Ajimaru/OctoScale/assets/stl-previews/OctoScale_Top.png

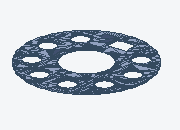
assets/stl-previews/OctoScale_Top.png
