Ajimaru/OctoScale/assets/stl-previews/OctoScaleBottom.png

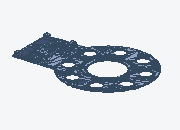
assets/stl-previews/OctoScaleBottom.png
