Ajimaru/OctoScale/assets/stl-previews/OctoScaleScreenBazel.png

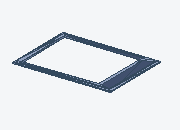
assets/stl-previews/OctoScaleScreenBazel.png
