Ajimaru/OctoScale/hardware/OctoScale-Wiring/OctoScale-Wiring.kicad_sch

## KiCad design hardware/OctoScale-Wiring/OctoScale-Wiring.kicad_sch (2026-09-16)

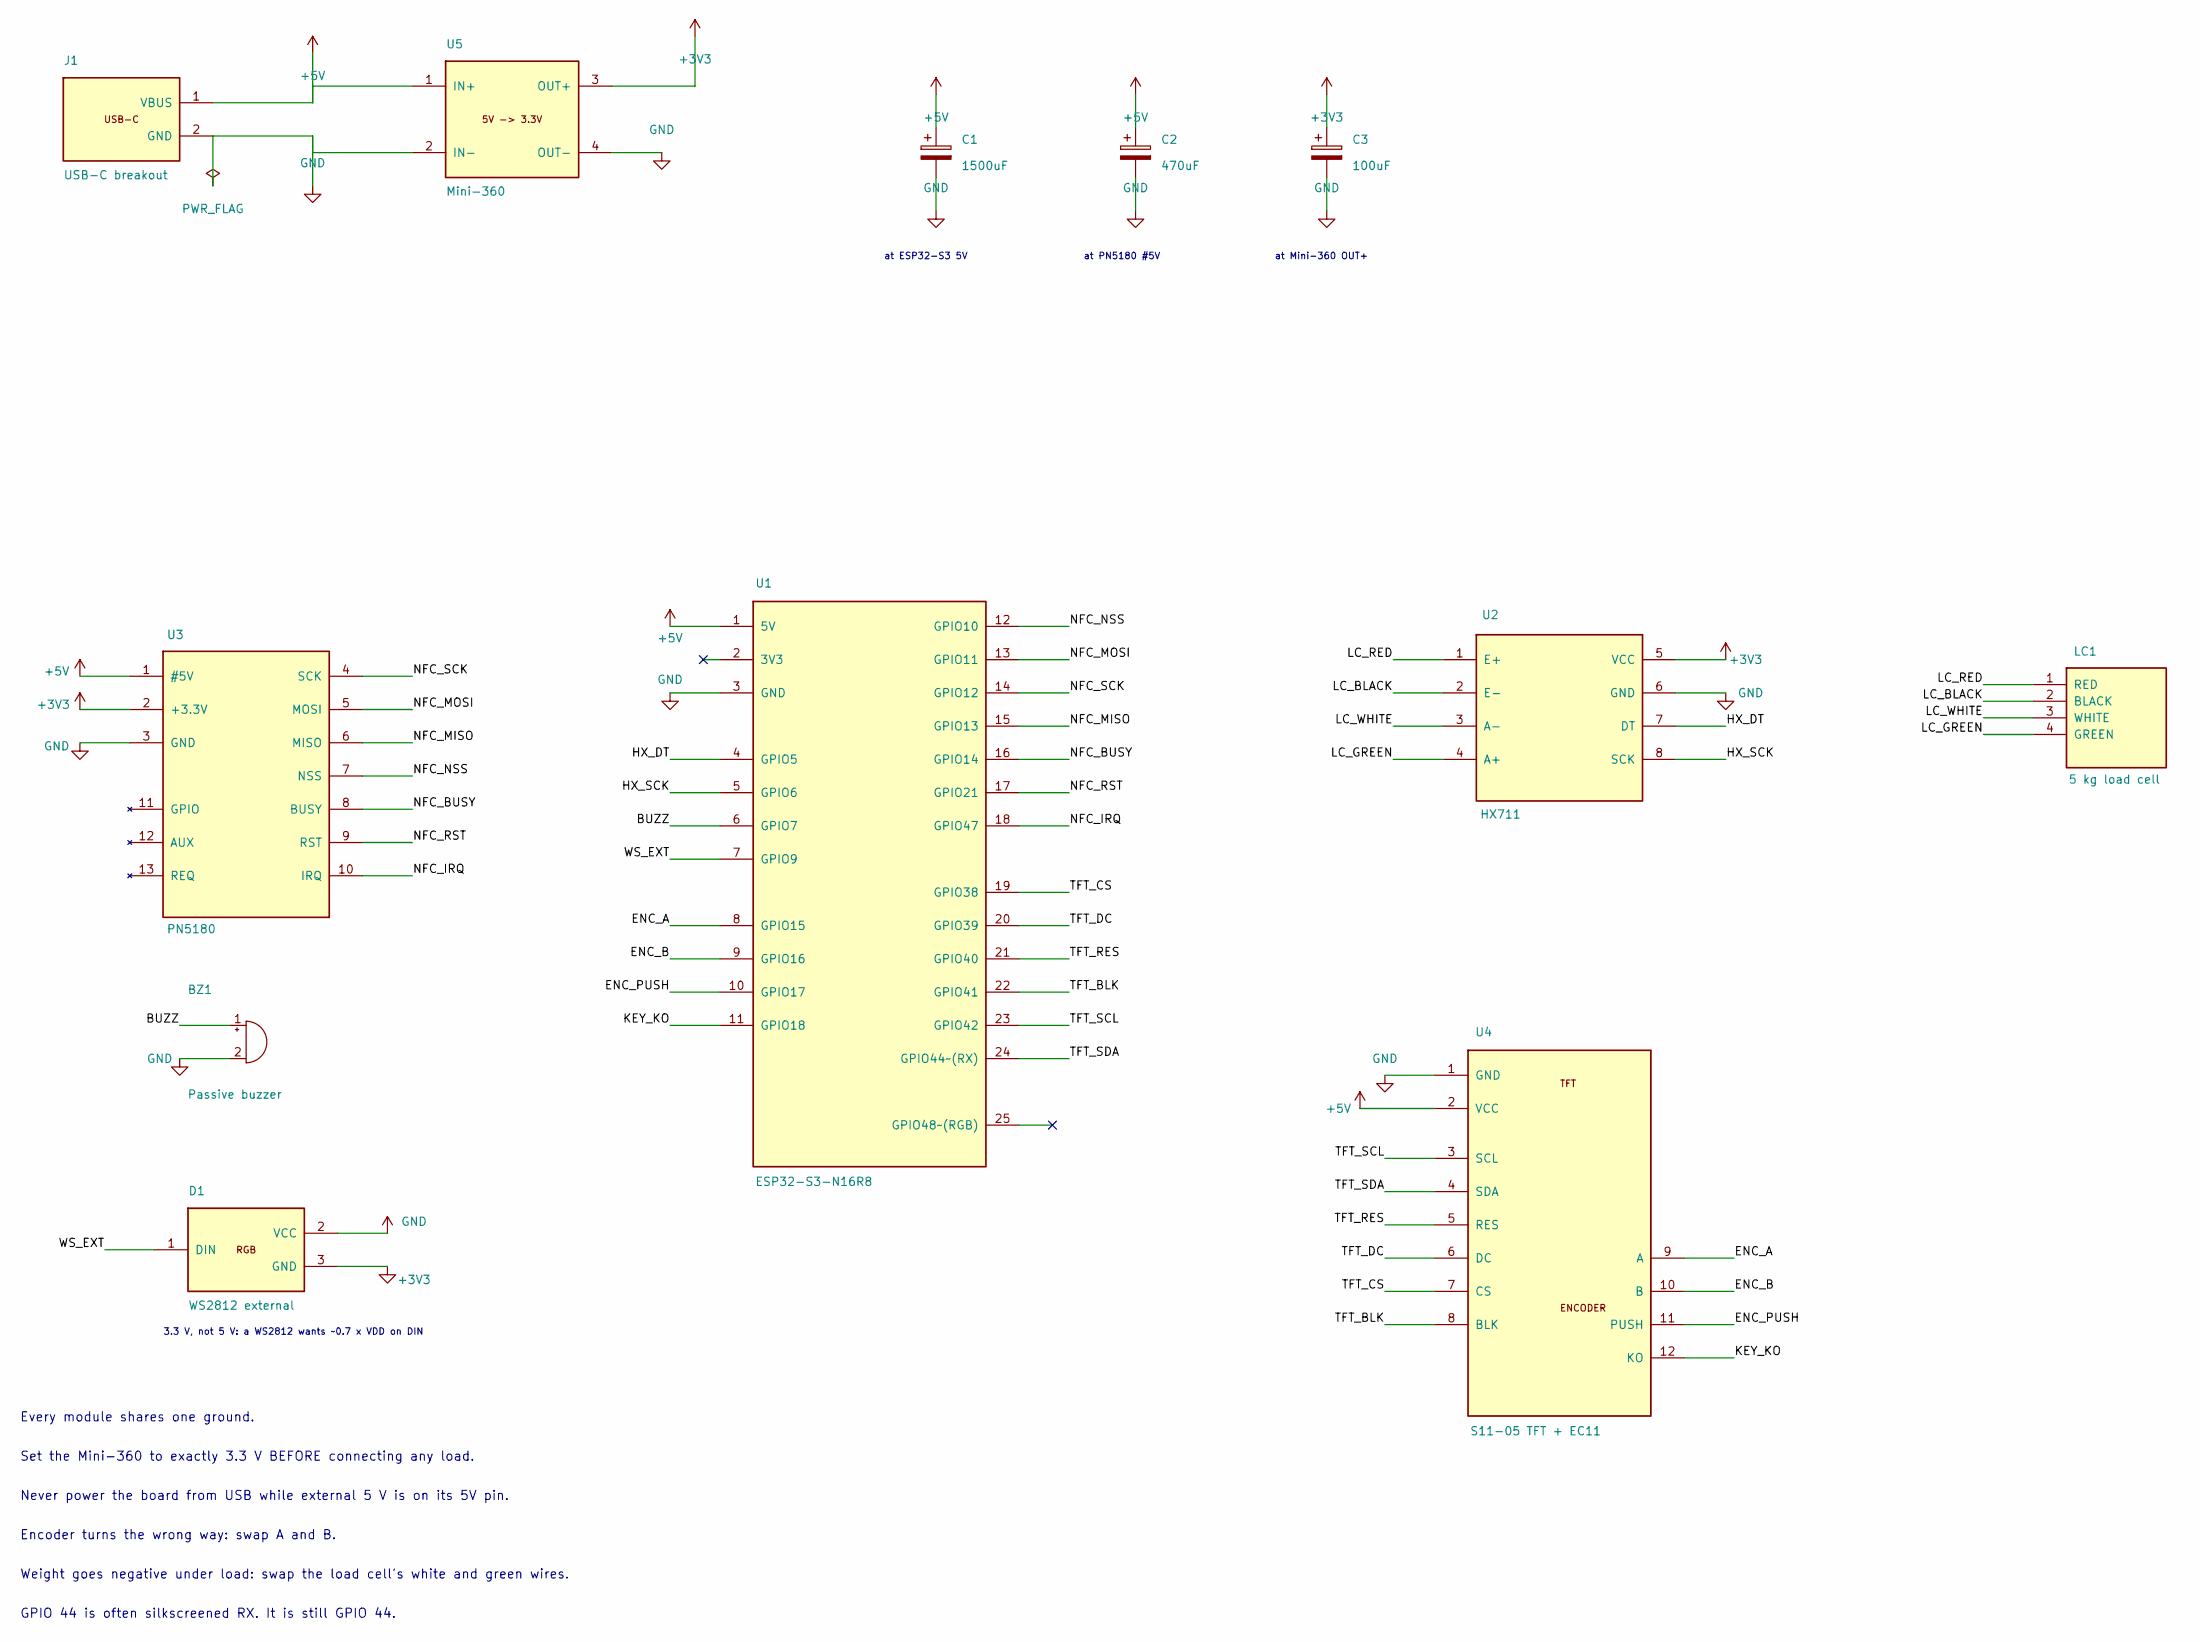
[picture p30: schematic OctoScale-Wiring.kicad_sch]

Parts:
BZ1: Passive buzzer
C1: 1500uF
C2: 470uF
C3: 100uF
D1: WS2812 external
J1: USB-C breakout
LC1: 5 kg load cell
U1: ESP32-S3-N16R8
U2: HX711
U3: PN5180
U4: S11-05 TFT + EC11
U5: Mini-360

Connections:
+3V3: C3.1, D1.2 (VCC), U2.5 (VCC), U3.2 (+3.3V), U5.3 (OUT+)
+5V: C1.1, C2.1, J1.1 (VBUS), U1.1 (5V), U3.1 (#5V), U4.2 (VCC), U5.1 (IN+)
BUZZ: BZ1.1 (+), U1.6 (GPIO7)
ENC_A: U1.8 (GPIO15), U4.9 (A)
ENC_B: U1.9 (GPIO16), U4.10 (B)
ENC_PUSH: U1.10 (GPIO17), U4.11 (PUSH)
GND: BZ1.2 (-), C1.2, C2.2, C3.2, D1.3 (GND), J1.2 (GND), U1.3 (GND), U2.6 (GND), U3.3 (GND), U4.1 (GND), U5.2 (IN-), U5.4 (OUT-)
HX_DT: U1.4 (GPIO5), U2.7 (DT)
HX_SCK: U1.5 (GPIO6), U2.8 (SCK)
KEY_KO: U1.11 (GPIO18), U4.12 (KO)
LC_BLACK: LC1.2 (BLACK), U2.2 (E-)
LC_GREEN: LC1.4 (GREEN), U2.4 (A+)
LC_RED: LC1.1 (RED), U2.1 (E+)
LC_WHITE: LC1.3 (WHITE), U2.3 (A-)
NFC_BUSY: U1.16 (GPIO14), U3.8 (BUSY)
NFC_IRQ: U1.18 (GPIO47), U3.10 (IRQ)
NFC_MISO: U1.15 (GPIO13), U3.6 (MISO)
NFC_MOSI: U1.13 (GPIO11), U3.5 (MOSI)
NFC_NSS: U1.12 (GPIO10), U3.7 (NSS)
NFC_RST: U1.17 (GPIO21), U3.9 (RST)
NFC_SCK: U1.14 (GPIO12), U3.4 (SCK)
TFT_BLK: U1.22 (GPIO41), U4.8 (BLK)
TFT_CS: U1.19 (GPIO38), U4.7 (CS)
TFT_DC: U1.20 (GPIO39), U4.6 (DC)
TFT_RES: U1.21 (GPIO40), U4.5 (RES)
TFT_SCL: U1.23 (GPIO42), U4.3 (SCL)
TFT_SDA: U1.24 (GPIO44~(RX)), U4.4 (SDA)
WS_EXT: D1.1 (DIN), U1.7 (GPIO9)

Notes on the sheet:
Weight goes negative under load: swap the load cell's white and green wires.
Set the Mini-360 to exactly 3.3 V BEFORE connecting any load.
at PN5180 #5V
Every module shares one ground.
at ESP32-S3 5V
Never power the board from USB while external 5 V is on its 5V pin.
Encoder turns the wrong way: swap A and B.
GPIO 44 is often silkscreened RX. It is still GPIO 44.
at Mini-360 OUT+
3.3 V, not 5 V: a WS2812 wants ~0.7 x VDD on DIN
