Ajimaru/OctoScale/src/pn5180nfc.h

#pragma once
#include <Arduino.h>

// pn5180nfc.h — PN5180 NFC reader (SPI) via the atrappmann/PN5180 library.
//
// FSPI bus (global SPI, SCK=12/MOSI=11/MISO=13), dedicated control pins
// (NSS=10/BUSY=14/RST=21). The chip answers over MISO, so the EEPROM version read
// confirms bus + chip + wiring all work.

// --- Tag types (protocol-neutral) ---
enum PN5180TagType {
  PN5180_TAG_NONE = 0,   // no tag in the field
  PN5180_TAG_NFCV,       // ISO15693 / NFC-V
  PN5180_TAG_NFCA,       // ISO14443-A / NFC-A
};

// Result of a debug probe (latest state, readable via HTTP).
struct PN5180ProbeResult {
  PN5180TagType type = PN5180_TAG_NONE;
  String uid = "";       // big-endian hex (usual display order)
  uint16_t atqa = 0;     // NFC-A only: ATQA (2 bytes)
  uint8_t sak = 0;       // NFC-A only: SAK (1 byte, type hint)
  uint8_t blockSize = 0; // NFC-V only: bytes/block (from getSystemInfo, 0 = unknown)
  uint8_t numBlocks = 0; // NFC-V only: block count (from getSystemInfo, 0 = unknown)
  uint8_t dsfid = 0;      // NFC-V only: Data Storage Format Identifier, if the tag reports one
  bool dsfidPresent = false;
  uint8_t afi = 0;        // NFC-V only: Application Family Identifier, if the tag reports one
  bool afiPresent = false;
  // NFC-V only: manufacturer-specific IC reference byte. Shown as a raw hex value, not
  // decoded to a chip name -- no verified public mapping of this byte to NXP ICODE
  // variants (SLI/SLIX/SLIX2/SLIX-L/...) was found; guessing wrong would be worse than
  // not showing a product name at all (see HARDWARE.md's "Tags evaluated for NFC-V").
  uint8_t icRef = 0;
  bool icRefPresent = false;
  int numPages = 0;       // NFC-A only: page/block count (Mifare Classic: fixed 64; NTAG: from GET_VERSION)
  bool numPagesPresent = false;
  long idParsed = -1;    // databaseId parsed off the tag's data area (-1 = none/unparsable)
  String idText = "";    // raw characters read where the databaseId would be (debug only)
  // How much the idParsed above can be trusted -- the legacy ID layout carries no magic
  // and no checksum, so "there are digits at the right offset" is NOT proof the tag is
  // ours. Consumers (the load flow, the SpoolManager plugin) need to tell the two apart:
  //   "extended" -- id came from a self-describing format (ntagExtended's "OX" magic,
  //                 octoscaleExtended's "OS", nfcvExtended, OpenSpool NDEF, TigerTag).
  //                 A magic matched, so the id is as trustworthy as the format itself.
  //   "legacy"   -- id came from the header-less ASCII field written by /nfcwriteid
  //                 (pn5180WriteNtagId & friends). Shape-validated only. A foreign tag
  //                 with digits in the same place is indistinguishable from ours.
  //   "unverified" -- as "legacy", AND the tag's occupancy says "foreign": the CC/data
  //                 area belongs to a format we did not write. Almost certainly not our
  //                 id. Callers should refuse to act on it without asking the user.
  //   "extendedNoId" -- a verified format that carries no OctoScale databaseId at all
  //                 (TigerTag, OpenPrintTag). Structured data IS present, so this is
  //                 NOT the same as "": a caller must not treat the tag as blank.
  //   ""         -- no id parsed at all (idParsed == -1).
  // Set by pn5180ApplyIdTrust() once occupancy is known; the raw read paths only ever
  // produce "extended" or "legacy", since they cannot see the CC.
  String idSource = "";
  // Capability Container state (NFC-A/NTAG + NFC-V only -- Mifare Classic has no CC
  // concept, stays ""). "virgin" = all-zero, never written; "ndef" = valid NDEF CC
  // (0xE1/0xE2 magic) -- the OTP bit is set and can NEVER be unset again, even by an
  // erase (see pn5180NtagCcIsVirgin/pn5180NfcvCcIsVirgin, and pn5180EraseTag's
  // comment); "other" = neither (foreign/non-NDEF content, erase/write would refuse
  // to touch it); "" = not read (Mifare, or read failed).
  String ccState = "";
  // False while a tag has been detected but its Extended read / occupancy probes have
  // not finished yet. The poll loop publishes type and uid as soon as the tag answers,
  // because the TFT needs them immediately, but the id and the format fields are only
  // filled a few hundred milliseconds later. Without this flag that window is
  // indistinguishable from a finished read of a tag that genuinely has no id, so a
  // caller polling once could see an Extended tag as "empty, no id" and offer to
  // overwrite it. A caller that only acts on complete data should require this.
  bool complete = false;
};

// databaseId storage on the tag (uniformly ASCII decimal):
//  - NFC-A/NTAG: user pages starting at page 4 (READ 0x30 always returns 4 pages/16 B).
//  - NFC-V/ISO15693: blocks starting at block 0 (readSingleBlock, usually 4 B/block).
// 12 bytes covers the full uint32 range (max 10 digits) + terminator.
static const uint8_t PN5180_ID_START_PAGE = 4;   // NFC-A: first user page
static const uint8_t PN5180_ID_START_BLOCK = 0;  // NFC-V: first data block
static const uint8_t PN5180_ID_BYTES = 12;       // 12 bytes ASCII decimal

// --- Mifare Classic 1K (blank/factory tags only -- see pn5180nfc.h's mifare section) --
// Block 4 = sector 1's first data block: sector 0 (blocks 0-3) holds the manufacturer
// block + often factory data, so sector 1 is the first "clean" sector on every blank
// 1K tag. One 16-byte block comfortably fits PN5180_ID_BYTES (12) -> no multi-block
// split needed, unlike NTAG's 4-byte pages.
static const uint8_t MIFARE_ID_BLOCK = 4;
static const uint8_t MIFARE_KEY_A[6] = {0xFF, 0xFF, 0xFF, 0xFF, 0xFF, 0xFF};  // factory default
static const uint8_t MIFARE_AUTH_KEY_A = 0x60;
static const uint8_t MIFARE_AUTH_KEY_B = 0x61;  // foreign tags may guard data with B

// --- Mifare Classic Extended layout (plan C.1) --------------------------------
// Sector 1 (block 4, unchanged) stays the legacy ID anchor. Sector 2 (blocks 8-9) adds
// numeric fields + a CRC-8 "commit marker" (block 8's magic). Sector 3 (blocks 12-14)
// adds strings. Block 8 is written LAST -- an aborted write leaves a tag with no magic,
// which reads back as "legacy ID only", never as a corrupt Extended payload.
static const uint8_t MIFARE_EXT_MAGIC0 = 'O';
static const uint8_t MIFARE_EXT_MAGIC1 = 'S';
// v3: sector 4 block 16 adds 7 more numeric fields (remainingWeight/totalLength/
// usedLength/firstUse/lastUse/purchasedOn/cost), sectors 5-8 (12 blocks) add a
// second, longer string buffer (code/batchNumber/purchasedFrom/finish/displayName),
// sector 9 block 36 is a v3-only commit marker (own sub-magic, checked independently
// of block 8's) so a v3 reader can tell "v3 fields genuinely present and intact" apart
// from "v3 version byte was set but the write was cut off before the new blocks
// landed" -- block 8 is still written LAST overall, same discipline as v1/v2.
static const uint8_t MIFARE_EXT_VERSION = 0x05;  // v5: drying/td in block 17[6..11] (v4: multi-colour in block 10[2..8])
static const uint8_t MIFARE_EXT_BLOCK8  = 8;
static const uint8_t MIFARE_EXT_BLOCK9  = 9;
static const uint8_t MIFARE_EXT_BLOCK10 = 10;  // v2+: [0] bed temp min [1] bed temp max
static const uint8_t MIFARE_EXT_BLOCK12 = 12;
static const uint8_t MIFARE_EXT_BLOCK13 = 13;
static const uint8_t MIFARE_EXT_BLOCK14 = 14;
static const int MIFARE_EXT_STRING_BYTES = 48;  // blocks 12-14, 16 bytes each
static const uint8_t MIFARE_EXT_BLOCK16 = 16;   // v3: sector 4, 7 packed numeric fields
// Block 16 is packed full (all 16 bytes), so the minute-of-day companions for
// firstUse/lastUse/purchasedOn get block 17 -- same sector, so it rides along on the
// auth block 16 already did, no extra Crypto1 round.
static const uint8_t MIFARE_EXT_BLOCK17 = 17;   // v3: 3x minute-of-day (uint16 LE);
                                               // v5: +6 dryTemp u8, +7 pad, +8 dryTime u16 LE,
                                               // +10 td x100 u16 LE, +12..15 reserved 0x00
// v3 string buffer: sectors 5-8, 12 contiguous data blocks treated as one flat
// 192-byte length-prefixed buffer (same [1-byte len][UTF-8 bytes] convention as the
// existing 3-string block above, just longer/more records). Block numbers skip each
// sector's trailer (23,27,31,35 are Crypto1 key blocks, not data).
static const uint8_t MIFARE_EXT_BLOCK20 = 20;
static const int MIFARE_EXT_STRING2_BLOCKS[12] = {20,21,22, 24,25,26, 28,29,30, 32,33,34};
static const int MIFARE_EXT_STRING2_BYTES = 192;  // 12 blocks x 16 B
static const uint8_t MIFARE_EXT_BLOCK36 = 36;   // v3: sector 9, commit marker

// --- NFC-V/ISO15693 Extended layout (blank/user-purchased tags only, same caveat as
// Mifare above -- this is NOT written to a tag whose blocks might already hold
// factory/vendor data; pn5180WriteNfcvSpoolTag only ever gets called for tags the
// user chose to write a spool ID to via the web UI in the first place). --------------
// Fixed 4-byte blocks (pn5180WriteNfcvId's own reasoning: getSystemInfo() has a known
// OOB-read bug on short/non-conforming replies, so it's never queried for this format
// either -- 4 B/block is the documented fallback and covers the ICODE-family tags this
// project targets). Blocks 0-2 stay the legacy 12-byte ID anchor (unchanged). Same
// commit-marker discipline as Mifare: the magic block is written LAST.
//   Block 3-4  (8 B):  magic(2) + version(1) + flags(1) + databaseId(4, uint32 LE)
//   Block 5-6  (8 B):  totalWeight/spoolWeight/usedWeight (uint16 LE each) + density (uint16 LE)
//   Block 7-10 (16 B): diameter+diameterTolerance (uint16 LE each) + 3 temps (uint8) +
//                      3 signed offsets (int8) + RGB (3 B) + hotend temp min/max (uint8 each,
//                      v2+) + CRC-8 (1 B, over blocks 3-10 minus the CRC byte itself)
//   Block 11-22 (48 B): strings (vendor/material/colorName), same length-prefixed layout as Mifare
//   Block 23 (4 B, v2+): [0] bed temp min (uint8) [1] bed temp max (uint8) [2-3] reserved
static const uint8_t NFCV_EXT_MAGIC0 = 'O';
static const uint8_t NFCV_EXT_MAGIC1 = 'S';
static const uint8_t NFCV_EXT_VERSION = 0x04;  // v4: drying/td in blocks 26-27 (v3: multi-colour in blocks 24-25)
static const uint8_t NFCV_EXT_BLOCK_START = 3;   // magic/version/flags/dbId: blocks 3-4
static const uint8_t NFCV_EXT_BLOCK_NUM   = 5;   // weights/density: blocks 5-6
static const uint8_t NFCV_EXT_BLOCK_PHYS  = 7;   // diameter/temps/rgb/crc: blocks 7-10
static const uint8_t NFCV_EXT_BLOCK_STR   = 11;  // strings: blocks 11-22
static const int NFCV_EXT_STRING_BYTES = 48;
static const uint8_t NFCV_EXT_BLOCK_TEMPRANGE = 23;  // v2+: bed temp min/max (4 B block)
// v3: multi-colour. tempRangeBuf has only [2..3] free -- not enough for 2 RGB trios plus
// flags -- so this takes two fresh blocks from the tag's unused tail (24-27 are free on
// the smallest ICODE this project targets, 28 blocks / 112 B). Colour 1 stays in
// physBuf where it always was.
static const uint8_t NFCV_EXT_BLOCK_COLOR = 24;   // [0..2] colour 2, [3] flags
                                                  // block 25: [0..2] colour 3, [3] reserved
// v4: drying/td. Strings live in blocks 11-22, i.e. BEFORE these -- unlike NTAG, adding
// them shifts nothing, so no existing field can be misread if a writer gets it wrong.
static const uint8_t NFCV_EXT_BLOCK_DRY = 26;    // [0] dryTemp u8, [1] pad, [2..3] dryTime u16 LE
                                                  // block 27: [0..1] td x100 u16 LE, [2..3] reserved
static const uint8_t NFCV_BLOCK_SIZE = 4;

// --- NTAG Extended layout (NTAG215/216 only -- 213's ~144 B usable can't fit the v3
// field set, see the capacity comment on pn5180WriteNtagExtended; offered as a
// SpoolManagerExtended write-format preference alongside openSpool, mirroring NFC-V's existing
// nfcvExtended/nfcvOpenSpool choice). No NDEF wrapper (Extended isn't meant to be read
// by a generic phone NFC app, same reasoning as Mifare's own Extended format) -- pages
// are written directly starting at page 4 (the first user page; pages 0-3 are
// UID/lock/CC/internal and never touched). Single version, full v3 field set from the
// start (no v1/v2 predecessor to stay compatible with, unlike Mifare/NFC-V). All 20
// fixed-layout bytes below are 4-byte-page-aligned (5 pages, 4-19 is NOT used -- pages
// 4-8, 20 B total) -------------------------------------------------------------------
//   Pages 4-5   (8 B):  magic(2) + version(1) + flags(1) + databaseId(4, uint32 LE)
//   Pages 6-7   (8 B):  totalWeight/spoolWeight/usedWeight/remainingWeight (uint16 LE each)
//   Page 8      (4 B):  density(uint16 LE) + diameter(uint16 LE)
//   Pages 9-11  (12 B): diameterTolerance(uint16 LE) + 3 temps(uint8) + 3 signed
//                       offsets(int8) + RGB(3 B) + temperatureMax(uint8)
//   Page 12     (4 B):  temperatureMin/bedTemperatureMin/bedTemperatureMax(uint8 each)
//                       + reserved(1 B)
//   Page 13     (4 B):  CRC-8(1 B, over pages 4-12 + this page's first byte, i.e. all
//                       fixed numeric bytes before it) + reserved(3 B)
//   Pages 14-16 (12 B): totalLength/usedLength (uint24 LE each, 6 B) + cost (uint16 LE,
//                       fixed-point x100, 2 B) + firstUse(uint16 LE, 2 B) + reserved(2 B)
//   Pages 17-18 (8 B):  lastUse/purchasedOn (uint16 LE each, days since 1970-01-01)
//   Pages 19+   :       8 length-prefixed strings (vendor/material/colorName/code/
//                       batchNumber/purchasedFrom/finish/displayName), same
//                       [1-byte len][UTF-8 bytes] convention as Mifare/NFC-V, flat
//                       across as many pages as the tag's capacity allows
//   Last page used: commit marker, own sub-magic ('N','X') + flags2 bit0 ("strings
//                       present") -- written LAST, same discipline as every other
//                       Extended format: an aborted write never reads back as corrupt,
//                       only as "no Extended data" (magic missing) or "numeric fields
//                       only, no strings" (commit marker missing/incomplete).
static const uint8_t NTAG_EXT_MAGIC0 = 'O';
static const uint8_t NTAG_EXT_MAGIC1 = 'X';
static const uint8_t NTAG_EXT_VERSION = 0x03;  // v3: drying/td on pages 21-22 (v2: multi-colour on pages 19-20)
static const uint8_t NTAG_EXT_PAGE_START = 4;    // magic/version/flags/dbId: pages 4-5
static const uint8_t NTAG_EXT_PAGE_NUM   = 6;    // totalWeight/spoolWeight/usedWeight/remainingWeight: pages 6-7
static const uint8_t NTAG_EXT_PAGE_DENSITY = 8;  // density+diameter: page 8
static const uint8_t NTAG_EXT_PAGE_PHYS  = 9;    // diameterTolerance/temps/offsets/rgb/temperatureMax: pages 9-11
static const uint8_t NTAG_EXT_PAGE_TEMPMIN = 12; // temperatureMin/bedTemperatureMin/Max: page 12
static const uint8_t NTAG_EXT_PAGE_CRC   = 13;   // CRC-8: page 13
static const uint8_t NTAG_EXT_PAGE_LEN   = 14;   // totalLength/usedLength/cost/firstUse: pages 14-16
static const uint8_t NTAG_EXT_PAGE_DATES = 17;   // lastUse/purchasedOn: pages 17-18
static const uint8_t NTAG_EXT_PAGE_COLOR = 19;  // v2: [0..2] colour 2, [3] flags
                                                // page 20: [0..2] colour 3, [3] reserved
// v3: pages 21-22 carry drying/td, so the string buffer moves 21 -> 23. This constant is
// the single source of truth for that boundary -- fixedBuf's size, the string budget, the
// pad loop and the commit-marker scan are all derived from it, so moving it moves them
// all together. Leaving strings at 21 while writing v3 would produce a complete,
// valid-LOOKING tag with the drying bytes read back as vendor/material.
static const uint8_t NTAG_EXT_PAGE_STR   = 23;  // strings start here (19 pre-v2, 21 in v2)
static const uint8_t NTAG_EXT_PAGE_DRY   = 21;  // v3: [0] dryTemp u8, [1] pad, [2..3] dryTime u16 LE
                                                //     page 22: [0..1] td x100 u16 LE, [2..3] reserved
static const uint8_t NTAG_EXT_MAGIC2_0 = 'N';    // commit marker sub-magic (last page)
static const uint8_t NTAG_EXT_MAGIC2_1 = 'X';
// CRC coverage: pages 4-12 (36 B) + page 13's own first byte position is the CRC
// itself, so coverage is exactly pages 4-12 -- 9 pages x 4 B = 36 B.
static const int NTAG_EXT_CRC_LEN = (NTAG_EXT_PAGE_CRC - NTAG_EXT_PAGE_START) * 4;

// --- TigerTag Standard layout (foreign format, NOT our own -- byte-for-byte per the
// TigerTag-SDK-Python, Apache-2.0, tigertag/tag.py, as relayed by the SpoolManagerExtended
// peer session and cross-checked against their own tested read-parser). All
// multi-byte fields BIG-ENDIAN, unlike every OctoScale-native NTAG/Mifare layout
// above (little-endian) -- do not reuse pn5180ScaleU16/pn5180ScaleU24 here, their
// byte order is wrong for this format.
//
// Payload is exactly 80 bytes (pages 4-23, NTAG213-sized, unsigned/"Standard"
// variant) -- offsets below are relative to page 4 = byte 0. Bytes 32+ (Twin-Tag-ID,
// Color 2/3, TD, custom message, measure-available) are NOT written: no verified
// SDK source for their layout was available at implementation time (see the
// TigerTag write-support conversation) -- leaving them zeroed is the deliberate
// choice over guessing.
static const uint8_t TIGERTAG_PAGE_START = 4;
static const uint32_t TIGERTAG_MAGIC_STANDARD = 0x5BF59264;  // unsigned, what we write
// static const uint32_t TIGERTAG_MAGIC_PLUS = 0xBC0FCB97;  // signed variant -- never
// written here, would need a private key we don't have.
static const uint32_t TIGERTAG_PRODUCT_ID_GENERIC = 0xFFFFFFFF;  // "offline"/no catalog link
static const int TIGERTAG_PAYLOAD_LEN = 80;                      // bytes, pages 4-23

// Data carried between the HTTP handler (POST /nfcwritespool) and the write functions.
// Optional fields use hasX flags (JSON may omit some) -- unset numeric fields are
// written as their "not set" sentinel (0xFFFF for uint16 scaled fields, matching the
// existing octoprint.h convention of -1 meaning "not set").
struct SpoolTagData {
  long databaseId = -1;
  String material = "", vendor = "", colorName = "";
  String color = "";       // "#rrggbb" or "#rrggbb;#rrggbb..." or "rainbow"/"transparent..."
  // v4 multi-color: SpoolManagerExtended's `color` field is a small grammar, not a hex
  // string -- "[transparent:]#hex[;#hex[;#hex]]" or the bare sentinel "rainbow" (see
  // its SPOOLMANAGER_UTILS.composeSpoolColor/parseSpoolColor). Up to THREE colours (the
  // UI has three pickers), plus two independent flags. Earlier formats stored only the
  // first colour and dropped the rest silently; these fields carry the whole value.
  // colorCount 0 with isTransparent set is legitimate ("transparent", untinted).
  uint8_t colorRgb[3][3] = {{0,0,0},{0,0,0},{0,0,0}};  // up to 3 colours, RGB each
  uint8_t colorCount = 0;      // how many of colorRgb[] are valid (0-3)
  bool isTransparent = false;  // "transparent:" prefix
  bool isRainbow = false;      // bare "rainbow" sentinel
  float diameter = -1;     // mm
  float diameterTolerance = -1;
  float density = -1;      // g/cm^3
  float totalWeight = -1, spoolWeight = -1, usedWeight = -1;  // g
  int temperature = -1, bedTemperature = -1, enclosureTemperature = -1;      // deg C
  int offsetTemperature = 0, offsetBedTemperature = 0, offsetEnclosureTemperature = 0;  // signed, deg C
  // Optional range around temperature/bedTemperature (SpoolManagerExtended's minTemperature/
  // maxTemperature/minBedTemperature/maxBedTemperature) -- temperature/bedTemperature
  // themselves stay the independent "target" value, not the range's min.
  int temperatureMin = -1, temperatureMax = -1;
  int bedTemperatureMin = -1, bedTemperatureMax = -1;
  // octoscaleExtended v3 fields (Mifare Classic 1K only so far -- see MIFARE_EXT_BLOCK16
  // and the v3 string buffer). -1/"" = not set, same convention as every other field.
  float remainingWeight = -1;              // g
  long totalLength = -1, usedLength = -1;  // mm
  String code = "", batchNumber = "", purchasedFrom = "", finish = "", displayName = "";
  long firstUse = -1, lastUse = -1, purchasedOn = -1;  // days since 1970-01-01
  // Time of day for the three dates above, 0..1439 (-1 = not set), stored SEPARATELY
  // from the day count rather than folded into it. SpoolManagerExtended's dates carry a real
  // time (13 of 13 used spools in their test DB had one), which used to be truncated on
  // write -- so every rewrite of an unchanged spool showed a date diff. Minutes since
  // the epoch would be the obvious encoding and is the one to avoid: it is ~29.8M today,
  // and these fields go over the wire as uint16, so pn5180ScaleU16 would clamp every
  // single value to 0xFFFF ("not set") and silently drop the date along with the time.
  // Keeping day and minute apart also means an older reader still sees exactly the day
  // it always saw, instead of a half-understood combined value.
  int firstUseMinuteOfDay = -1, lastUseMinuteOfDay = -1, purchasedOnMinuteOfDay = -1;
  float cost = -1;                          // 2 decimal places

  // Drying fields (OpenPrintTag spec keys 57/58) plus td (key 27). No octoscaleExtended
  // layout carries any of them. OPT carries all three; TigerTag carries the two drying
  // fields (bytes 28/29) but not td.
  //
  // dryingTime is in MINUTES everywhere on THIS side of the boundary -- the OPT spec
  // unit, and what /nfcprobe reports and /nfcwritespool accepts. Per-layout conversion
  // is the individual writer's job: OPT stores minutes verbatim, TigerTag's byte 29 is
  // HOURS and divides (see pn5180WriteNtagTigerTag). Do not "simplify" that division
  // away -- without it every TigerTag drying time is off by a factor of 60, which is
  // exactly the bug that was measured on hardware (3h written -> 180 in byte 29).
  int dryingTemperature = -1;   // deg C
  int dryingTime = -1;          // minutes (spec unit; 8 h arrives here as 480)
  // Transmission distance: a DIMENSIONLESS opacity number (0.1 = most opaque,
  // 100 = most transparent), not a length. Never label it mm.
  float td = -1;

  // TigerTag-only: pre-resolved IDs into TigerTag's own Material/Brand/Aspect/Type/
  // Diameter/MeasureUnit registries. The firmware does NOT own or look up this
  // registry -- the caller (SpoolManagerExtended) resolves text values to these IDs before
  // sending, same "plugin resolves, firmware just packs bytes" split already used
  // for every other format. -1 = not resolved/not set.
  long tigerTagMaterialId = -1, tigerTagBrandId = -1, tigerTagAspectId = -1;
  long tigerTagTypeId = -1, tigerTagDiameterId = -1, tigerTagMeasureUnitId = -1;
};

// CRC-8, polynomial 0x07 (the plan's chosen poly), no reflection, init 0x00 -- a small,
// dependency-free implementation since none of this project's existing libraries
// expose a CRC-8.
inline uint8_t pn5180Crc8(const uint8_t *data, int len) {
  uint8_t crc = 0x00;
  for (int i = 0; i < len; i++) {
    crc ^= data[i];
    for (int b = 0; b < 8; b++)
      crc = (crc & 0x80) ? (uint8_t)((crc << 1) ^ 0x07) : (uint8_t)(crc << 1);
  }
  return crc;
}

// Parses the first color out of SpoolManagerExtended's `color` field: "#rrggbb", optionally
// followed by more colors separated by ';' (multi-color spools -- only the first is
// storable in the 3-byte RGB slot), or a sentinel like "rainbow"/"transparent[:#hex]"
// (neither has a single RGB value -- returns false, caller leaves the RGB bytes zeroed).
// Parses SpoolManagerExtended's full `color` grammar into the v4 fields. The single-
// colour pn5180ParseColorHex below stays as-is: every pre-v4 write path still uses it,
// and the primary colour must keep landing in the same 3-byte slot it always has.
//
//   "rainbow"                       -> rainbow flag, no colours
//   "transparent"                   -> transparent flag, no colours (untinted)
//   "transparent:#rgb[;#rgb[;#rgb]]"-> transparent flag + 1-3 colours
//   "#rgb[;#rgb[;#rgb]]"            -> 1-3 colours, opaque
//
// Anything unparseable leaves the outputs at "nothing set" rather than guessing --
// a wrong colour on a tag is worse than no colour, same reasoning as everywhere else.
// Packs the v4 colour flags into one byte, shared by all three carriers so the wire
// encoding cannot drift apart between them: bit0 transparent, bits1-2 colour count
// (0-3), bit3 rainbow. 0x00 therefore means "no colour information", which is exactly
// what a pre-v4 tag's zeroed reserve bytes read back as -- no separate presence flag
// needed.
inline bool pn5180ParseColorHex(const String &color, uint8_t rgbOut[3]);  // defined below

inline uint8_t pn5180PackColorFlags(const SpoolTagData &d) {
  uint8_t f = 0;
  if (d.isTransparent) f |= 0x01;
  f |= (uint8_t)((d.colorCount & 0x03) << 1);
  if (d.isRainbow) f |= 0x08;
  return f;
}
inline void pn5180UnpackColorFlags(uint8_t f, SpoolTagData &d) {
  d.isTransparent = (f & 0x01) != 0;
  d.colorCount = (uint8_t)((f >> 1) & 0x03);
  d.isRainbow = (f & 0x08) != 0;
}

inline void pn5180ParseColorGrammar(const String &color, uint8_t rgbOut[3][3],
                                    uint8_t &countOut, bool &transparentOut,
                                    bool &rainbowOut) {
  countOut = 0; transparentOut = false; rainbowOut = false;
  for (int i = 0; i < 3; i++) rgbOut[i][0] = rgbOut[i][1] = rgbOut[i][2] = 0;

  String c = color;
  c.trim();
  if (c.length() == 0) return;

  String lower = c; lower.toLowerCase();
  if (lower == "rainbow") { rainbowOut = true; return; }
  if (lower.startsWith("transparent")) {
    transparentOut = true;
    int colon = c.indexOf(':');
    if (colon < 0) return;          // bare "transparent", no base colours
    c = c.substring(colon + 1);
    c.trim();
  }

  // Split on ';' -- at most 3 colours are storable, extras are ignored (the UI only
  // offers three pickers, so a longer list would be malformed input rather than data).
  int start = 0;
  while (start < (int)c.length() && countOut < 3) {
    int sep = c.indexOf(';', start);
    String part = (sep < 0) ? c.substring(start) : c.substring(start, sep);
    part.trim();
    uint8_t rgb[3];
    if (pn5180ParseColorHex(part, rgb)) {
      rgbOut[countOut][0] = rgb[0]; rgbOut[countOut][1] = rgb[1]; rgbOut[countOut][2] = rgb[2];
      countOut++;
    }
    if (sep < 0) break;
    start = sep + 1;
  }
}

// Inverse of pn5180ParseColorGrammar: rebuilds the grammar string from the parsed
// parts. Must stay an exact mirror of the parser above, or a /nfcprobe result fed back
// into /nfcwritespool would not round-trip. "transparent" with zero colours is a
// legitimate state (untinted), see the colorCount comment on SpoolTagData.
inline String pn5180ComposeColorGrammar(const uint8_t rgb[3][3], uint8_t count,
                                        bool transparent, bool rainbow) {
  if (rainbow) return String("rainbow");   // parser returns early on it too, count ignored
  String out;
  if (transparent) out = "transparent";
  if (count == 0) return out;              // "" or bare "transparent"
  char hx[10];
  for (uint8_t i = 0; i < count && i < 3; i++) {
    snprintf(hx, sizeof(hx), "#%02X%02X%02X", rgb[i][0], rgb[i][1], rgb[i][2]);
    out += (i == 0) ? (transparent ? ":" : "") : ";";
    out += hx;
  }
  return out;
}

// Single decode point for the primary colour of the three Extended carriers.
//
// Why this exists rather than a condition at each read site: the primary colour's three
// bytes carry no "unset" encoding of their own -- black is 0,0,0, and so is an untouched
// buffer. The only authority on whether a colour was stored is the flag byte's
// colorCount (see pn5180PackColorFlags), and that byte lives in a different block/page
// that is itself version-gated and read further down. Deciding at the byte site is
// therefore guessing; this runs once the flags are actually in hand.
//
// haveFlags=false means the tag predates its carrier's flag byte (Mifare < v4,
// NFC-V < v3, NTAG < v2 -- the counters run per carrier and do NOT line up). There the
// information was never written, so black and unset are indistinguishable: fall back to
// the historic "non-zero means set" reading and leave 0,0,0 empty rather than inventing
// a black that could overwrite a real spool colour on import.
inline void pn5180ApplyExtendedColor(SpoolTagData &out, const uint8_t primary[3],
                                     bool haveFlags, uint8_t flagByte) {
  if (haveFlags) {
    pn5180UnpackColorFlags(flagByte, out);
    // colorCount==0 with isTransparent is valid ("transparent", untinted) -- must not
    // be overwritten with the zeroed primary bytes.
    if (out.colorCount >= 1)
      for (int i = 0; i < 3; i++) out.colorRgb[0][i] = primary[i];
  } else if (primary[0] || primary[1] || primary[2]) {
    for (int i = 0; i < 3; i++) out.colorRgb[0][i] = primary[i];
    out.colorCount = 1;
  }
  // out.color stays the PRIMARY colour as plain "#RRGGBB" -- the full grammar is what
  // colorFull carries (see /nfcprobe). Widening this field would change a published
  // value the web UI displays.
  if (out.colorCount >= 1) {
    char hx[10];
    snprintf(hx, sizeof(hx), "#%02X%02X%02X",
             out.colorRgb[0][0], out.colorRgb[0][1], out.colorRgb[0][2]);
    out.color = hx;
  }
}

// Primary colour for the single-RGB slot every carrier has had since v1. Prefers the
// already-parsed grammar result (d.colorRgb[0]) over re-parsing d.color, because
// pn5180ParseColorHex alone returns false for "transparent:#ff0000;..." -- the string
// starts with 't', not '#'. That is exactly right for a plain hex parser and exactly
// wrong here: it silently dropped the primary colour of every transparent multi-colour
// spool, writing 0,0,0 while colours 2 and 3 came through fine.
inline bool pn5180PrimaryColorRgb(const SpoolTagData &d, uint8_t rgbOut[3]) {
  if (d.colorCount > 0) {
    for (int i = 0; i < 3; i++) rgbOut[i] = d.colorRgb[0][i];
    return true;
  }
  return pn5180ParseColorHex(d.color, rgbOut);  // pre-grammar callers / plain "#rrggbb"
}

inline bool pn5180ParseColorHex(const String &color, uint8_t rgbOut[3]) {
  if (color.length() < 7 || color[0] != '#') return false;  // sentinels don't start with '#'
  char buf[3] = {0, 0, 0};
  for (int i = 0; i < 3; i++) {
    buf[0] = color[1 + i*2]; buf[1] = color[2 + i*2];
    for (int c = 0; c < 2; c++) if (!isxdigit((unsigned char)buf[c])) return false;
    rgbOut[i] = (uint8_t)strtoul(buf, nullptr, 16);
  }
  return true;
}

// Truncates a UTF-8 string to at most maxBytes bytes WITHOUT cutting a multi-byte
// sequence in half (a continuation byte has the top two bits 10xxxxxx -- back off until
// the cut point isn't one).
inline String pn5180Utf8SafeTruncate(const String &s, int maxBytes) {
  if ((int)s.length() <= maxBytes) return s;
  int cut = maxBytes;
  while (cut > 0 && (((uint8_t)s[cut]) & 0xC0) == 0x80) cut--;
  return s.substring(0, cut);
}

inline const char *pn5180TagTypeName(PN5180TagType t) {
  switch (t) {
    case PN5180_TAG_NFCV: return "NFC-V (ISO15693)";
    case PN5180_TAG_NFCA: return "NFC-A (ISO14443-A)";
    default:              return "no tag";
  }
}

// Rough SAK interpretation (a hint only; a full read would need ATS). Good enough for
// the debug view. atqa/sak are the final values after the cascade completes.
inline const char *pn5180NfcaProduct(uint16_t atqa, uint8_t sak) {
  if (sak & 0x20) return "ISO14443-4 (smartcard/DESFire?)";
  // SAK 0x00 = type-2 tag (not ISO14443-4). ATQA bits 6-7 of the LSB = UID size.
  if ((sak & ~0x04) == 0x00) {
    uint8_t uidSize = (atqa >> 6) & 0x03;  // 0=4B (single), 1=7B (double), 2=10B (triple)
    if (uidSize == 1) return "NTAG / Ultralight (7-byte)";
    return "Type 2 (Ultralight-like)";
  }
  if (sak == 0x08) return "Mifare Classic 1K";
  if (sak == 0x18) return "Mifare Classic 4K";
  if (sak == 0x09) return "Mifare Mini";
  if (sak == 0x28) return "Mifare Classic (ISO14443-4)";
  return "Mifare/NFC-A";
}

#include <SPI.h>
#include <PN5180.h>
#include <PN5180ISO15693.h>

// Pins defined in main.cpp, referenced here as extern.
extern const int PN5180_NSS;
extern const int PN5180_BUSY;
extern const int PN5180_RST;
extern const int SPI_SCK;
extern const int SPI_MOSI;
extern const int SPI_MISO;

static PN5180ISO15693 *g_pn5180 = nullptr;
static bool g_pn5180Ready = false;
static int g_pn5180LastRc = 999;      // last getInventory code (HTTP diagnostics)
static uint32_t g_pn5180OkCount = 0;  // total tags successfully read

// Initializes the PN5180 (ISO15693/NFC-V). Reads the chip version to verify it's alive
// and sets up the RF field. Returns true = the chip answered plausibly.
// Debug hook for PN5180::mifareAuthenticate (see PN5180.h) -- logs the raw send/recv
// frame bytes via our own debug console (fully inert while it's off, like all dbgLog*).
// Off by default even when the debug log is on: with a Mifare tag resting on the
// reader, the 500 ms poll authenticates every single time, so this callback alone
// produced TWO lines every 500 ms -- enough to churn through the whole ring buffer in
// minutes and bury everything else in it. Flip g_pn5180AuthTrace to true (via
// /nfcauthtrace?on=1) only while actually chasing an auth/Crypto1 problem.
volatile bool g_pn5180AuthTrace = false;
static void pn5180MifareAuthDebugCb(const uint8_t *sendBuf, size_t sendLen,
                                    const uint8_t *recvBuf, size_t recvLen, bool ok) {
  if (!g_dbgLogEnabled || !g_pn5180AuthTrace) return;
  String hex;
  char b[4];
  for (size_t i = 0; i < sendLen; i++) { snprintf(b, sizeof(b), "%02X ", sendBuf[i]); hex += b; }
  if (!recvBuf) {
    dbgLogf("Mifare auth SPI: TX %s", hex.c_str());
  } else {
    String rhex;
    for (size_t i = 0; i < recvLen; i++) { snprintf(b, sizeof(b), "%02X ", recvBuf[i]); rhex += b; }
    dbgLogf("Mifare auth SPI: TX %s RX %s ok=%d", hex.c_str(), rhex.c_str(), ok);
  }
}

inline bool pn5180Init() {
  // Start SPI with our pins (the library later calls SPI.begin() without pins, so we
  // set them beforehand; SS=-1, the library drives CS itself via NSS).
  SPI.begin(SPI_SCK, SPI_MISO, SPI_MOSI, -1);

  PN5180::mifareAuthDebugCb = pn5180MifareAuthDebugCb;

  g_pn5180 = new PN5180ISO15693((uint8_t)PN5180_NSS, (uint8_t)PN5180_BUSY, (uint8_t)PN5180_RST);
  g_pn5180->begin();
  g_pn5180->reset();

  uint8_t product[2] = {0, 0}, firmware[2] = {0, 0};
  g_pn5180->readEEprom(PRODUCT_VERSION, product, 2);
  g_pn5180->readEEprom(FIRMWARE_VERSION, firmware, 2);
  Serial.printf("PN5180: product %d.%d, firmware %d.%d\n",
                product[1], product[0], firmware[1], firmware[0]);

  uint16_t fw = (firmware[1] << 8) | firmware[0];
  if (fw == 0x0000 || fw == 0xFFFF) {
    Serial.println("PN5180: no plausible response (check SPI/wiring)");
    g_pn5180Ready = false;
    return false;
  }
  g_pn5180->setupRF();  // set up the RF field for ISO15693
  Serial.println("PN5180: ready (ISO15693/NFC-V, RF active)");
  g_pn5180Ready = true;
  return true;
}

inline bool pn5180IsReady() { return g_pn5180Ready; }
inline int pn5180LastRc() { return g_pn5180LastRc; }
inline uint32_t pn5180OkCount() { return g_pn5180OkCount; }

// --- Tag-type detection for debug mode --------------------------------------
// The PN5180 chip supports many protocols; the atrappmann library only covers
// ISO15693. For the debug menu, type detection is enough: try both common NFC
// families per poll and report whichever answered.
//   - NFC-V  (ISO15693): tags like ICODE SLIX, common spool tags.
//   - NFC-A  (ISO14443-A): NTAG21x, Mifare Ultralight/Classic, most phone tags.
// NFC-A is hand-built on the base class's low-level primitives (REQA->ATQA,
// anticollision->UID, SELECT->SAK). loadRFConfig indices for 106 kbps type-A: 0x00/0x80.

// Tries to read an ISO15693 tag. On success, writes the 8-byte UID as a hex string
// (big-endian, usual display order) to uidHexOut. Returns true = a tag is present.
// Non-blocking: no tag -> false, no delay.
inline bool pn5180ReadTag(String &uidHexOut) {
  uidHexOut = "";
  if (!g_pn5180Ready || !g_pn5180) return false;
  uint8_t uid[8] = {0};
  ISO15693ErrorCode rc = g_pn5180->getInventory(uid);
  g_pn5180LastRc = (int)rc;  // for HTTP diagnostics (/nfc5180)
  if (rc != ISO15693_EC_OK) {
    // A failed inventory leaves the RF state stuck -> reset + setupRF, otherwise no
    // tag is ever detected afterward (per the library's own example).
    g_pn5180->reset();
    g_pn5180->setupRF();
    return false;
  }
  g_pn5180OkCount++;
  char buf[3];  // UID arrives LSB-first -> reverse for the usual display order
  for (int i = 7; i >= 0; i--) {
    snprintf(buf, sizeof(buf), "%02X", uid[i]);
    uidHexOut += buf;
  }
  return true;
}

// Re-arms the RF field (if the reader got stuck after an error).
inline void pn5180Recover() {
  if (!g_pn5180) return;
  g_pn5180->reset();
  g_pn5180->setupRF();
}

// --- NFC-A (ISO14443-A) low-level probe -------------------------------------
// Implemented only as far as the debug menu needs: wake the card (REQA/WUPA), read
// ATQA, cascade-1 anticollision for the UID, SELECT for the SAK. No full ISO14443-4
// stack, no memory read — just type + UID.
//
// Uses the PN5180 base class's public low-level methods: loadRFConfig / setRF_on /
// setRF_off / sendData(with validBits) / readData / getIRQStatus / clearIRQStatus /
// readRegister. Returns true = an NFC-A card answered (out filled in).
//
// CRC registers: for ISO14443-A REQA/ATQA/anticollision, CRC MUST be OFF on both TX
// and RX (these frames carry no CRC, only parity). Without this the PN5180 discards
// the ATQA and the card is never detected. Bit 0 of each register is the CRC enable.
#ifndef CRC_TX_CONFIG
#define CRC_TX_CONFIG (0x19)
#endif

// Waits for the RX IRQ or a timeout (ms). true = data received.
static inline bool pn5180WaitRx(PN5180 *p, uint32_t timeoutMs) {
  uint32_t t0 = millis();
  while (millis() - t0 < timeoutMs) {
    if (p->getIRQStatus() & RX_IRQ_STAT) return true;
    delay(1);
  }
  return false;
}

// sendData() rejects the command if the chip isn't in WaitTransmit state yet (checked
// once, no retry inside the library). Right after the AndMask/OrMask register writes
// that request Idle->Transceive, the chip needs a moment to actually get there -> retry
// a few times with a short delay instead of failing the whole write on the first miss.
static inline bool pn5180SendDataRetry(PN5180 *p, uint8_t *data, int len, uint8_t validBits = 0) {
  for (int attempt = 0; attempt < 20; attempt++) {
    if (p->sendData(data, len, validBits)) return true;
    int state = (int)p->getTransceiveState();
    dbgLogf("  sendData retry %d: transceiveState=%d", attempt, state);
    // state 3/4/5 = still wait-receive/wait-for-data/receiving from the PREVIOUS
    // transceive cycle. Just re-arming Idle/Transceive doesn't clear it (confirmed:
    // stays stuck at state=3 for 20 straight retries) -> also clear IRQ status each
    // time, matching the full reset sequence used elsewhere (clearIRQStatus first).
    p->clearIRQStatus(0xffffffff);
    p->writeRegisterWithAndMask(SYSTEM_CONFIG, 0xfffffff8);  // Idle/StopCom
    delay(2);
    p->writeRegisterWithOrMask(SYSTEM_CONFIG, 0x00000003);   // Transceive
    delay(2);
  }
  return false;
}

inline bool pn5180ProbeNfcA(PN5180ProbeResult &out) {
  if (!g_pn5180) return false;
  PN5180 *p = g_pn5180;  // base-class pointer (public inheritance)

  // Reload RF for ISO14443-A/106k (switches out of the active ISO15693 mode).
  p->reset();
  if (!p->loadRFConfig(0x00, 0x80)) { return false; }  // 0x00 TX, 0x80 RX = type-A 106k
  if (!p->setRF_on()) { return false; }
  p->writeRegisterWithAndMask(SYSTEM_CONFIG, 0xfffffff8);  // arm transceive state
  p->writeRegisterWithOrMask(SYSTEM_CONFIG, 0x00000003);
  delay(2);

  p->writeRegisterWithAndMask(CRC_RX_CONFIG, 0xfffffffe);  // CRC off TX+RX
  p->writeRegisterWithAndMask(CRC_TX_CONFIG, 0xfffffffe);

  // --- REQA (0x26), 7 valid bits -> ATQA (2 bytes) ---
  p->clearIRQStatus(0xffffffff);
  p->writeRegisterWithAndMask(SYSTEM_CONFIG, 0xfffffff8);  // reset to idle->transceive
  p->writeRegisterWithOrMask(SYSTEM_CONFIG, 0x00000003);
  uint8_t reqa = 0x26;
  if (!p->sendData(&reqa, 1, 7)) { return false; }  // validBits=7 (short frame)
  if (!pn5180WaitRx(p, 15)) { return false; }       // no card
  uint32_t rxStatus = 0;
  p->readRegister(RX_STATUS, &rxStatus);
  uint16_t atqaLen = (uint16_t)(rxStatus & 0x1ff);
  if (atqaLen < 2) { return false; }
  uint8_t *atqa = p->readData(2);
  if (!atqa) { return false; }
  out.atqa = (uint16_t)atqa[0] | ((uint16_t)atqa[1] << 8);

  // --- Cascade loop (CL1=0x93, CL2=0x95) for the full UID + final SAK ---
  // 4-byte UID: CL1 only. 7-byte UID: CL1's response starts with CT=0x88 + UID[0..2],
  // CL1's SAK has bit2 set ("UID incomplete") -> CL2 returns UID[3..6]. Per cascade:
  // anticollision (CRC off) -> UID part, then SELECT (CRC on) -> SAK.
  const uint8_t selCode[2] = { 0x93, 0x95 };  // CL1, CL2
  uint8_t uidBytes[7];
  int uidCount = 0;
  char buf[3];
  out.uid = "";

  for (int cl = 0; cl < 2; cl++) {
    // -- Anticollision: CRC off, SEL + NVB=0x20 -> 5 bytes (4 UID/CT + BCC) --
    p->writeRegisterWithAndMask(CRC_RX_CONFIG, 0xfffffffe);
    p->writeRegisterWithAndMask(CRC_TX_CONFIG, 0xfffffffe);
    p->clearIRQStatus(0xffffffff);
    p->writeRegisterWithAndMask(SYSTEM_CONFIG, 0xfffffff8);
    p->writeRegisterWithOrMask(SYSTEM_CONFIG, 0x00000003);
    uint8_t anticoll[2] = { selCode[cl], 0x20 };
    if (!p->sendData(anticoll, 2, 0)) break;
    if (!pn5180WaitRx(p, 15)) break;
    p->readRegister(RX_STATUS, &rxStatus);
    uint16_t uidLen = (uint16_t)(rxStatus & 0x1ff);
    if (uidLen < 4) break;
    uint8_t *r = p->readData(5);   // 4 UID/CT bytes + BCC
    if (!r) break;

    // r[0..3] = UID part (a 7-byte UID's CL1 starts with CT=0x88).
    bool ct = (cl == 0 && r[0] == 0x88);  // cascade tag only in CL1 of a 7-byte UID
    for (int i = (ct ? 1 : 0); i < 4 && uidCount < 7; i++) {
      uidBytes[uidCount++] = r[i];
    }

    // -- SELECT: CRC on, SEL + 0x70 + 4 UID/CT bytes + BCC -> SAK --
    p->writeRegisterWithOrMask(CRC_RX_CONFIG, 0x00000001);
    p->writeRegisterWithOrMask(CRC_TX_CONFIG, 0x00000001);
    p->clearIRQStatus(0xffffffff);
    p->writeRegisterWithAndMask(SYSTEM_CONFIG, 0xfffffff8);
    p->writeRegisterWithOrMask(SYSTEM_CONFIG, 0x00000003);
    uint8_t sel[7] = { selCode[cl], 0x70, r[0], r[1], r[2], r[3], r[4] };
    if (!p->sendData(sel, 7, 0)) break;
    if (!pn5180WaitRx(p, 15)) break;
    p->readRegister(RX_STATUS, &rxStatus);
    if ((uint16_t)(rxStatus & 0x1ff) < 1) break;
    uint8_t *sakResp = p->readData(1);
    if (!sakResp) break;
    out.sak = sakResp[0];

    if (!(out.sak & 0x04)) break;  // SAK bit2 = UID incomplete -> next cascade
  }

  // Every failure above is a `break` out of the cascade loop, which leaves whatever
  // CL1 delivered in uidBytes -- typically 3 bytes (4 minus the 0x88 cascade tag).
  // Without this check that fragment was returned as a successful read: NFC-A UIDs are
  // 4 or 7 bytes, never 3, so it is structurally impossible yet looked valid to every
  // caller. Consequences seen in the field: it differed from g_lastUid, so the poll
  // treated it as a new tag and refilled the extended-read cache with unreadable data
  // (hasExtended 1 -> 0, id 103 -> -1 on a tag that never moved, plus a pointless
  // byCode HTTP lookup and a "spool gone" flicker on the TFT); and via g_pn5180Uid it
  // reached /nfcwritestatus, where SpoolManagerExtended derives rfidTagKey from it -- a
  // truncated UID yields a well-formed but WRONG key, which their teach-in wrote
  // straight to the database, permanently unlinking the tag. Report it as "no tag"
  // instead: a partial anticollision run is a failed read, not a new tag.
  if (uidCount != 4 && uidCount != 7) return false;

  for (int i = 0; i < uidCount; i++) {
    snprintf(buf, sizeof(buf), "%02X", uidBytes[i]);
    out.uid += buf;
  }

  out.type = PN5180_TAG_NFCA;
  return true;
}

// Forward declarations: the ID readers are defined further below (needed by both
// pn5180Probe, for the debug view, and pn5180ReadSpool, for the real read path).
inline bool pn5180ReadNtagId(long &idOut, String &textOut);
inline bool pn5180ReadNfcvId(const uint8_t *uidLsb, long &idOut, String &textOut);
inline bool pn5180ReadMifareId(const String &uidHex, long &idOut, String &textOut);
inline bool pn5180ReadMifareExtended(const String &uidHex, SpoolTagData &out);
inline bool pn5180ReadNtagOpenSpool(SpoolTagData &out);
inline bool pn5180ReadNtagExtended(SpoolTagData &out);
inline bool pn5180ReadNtagTigerTag(SpoolTagData &out);
inline bool pn5180ReadNfcvExtended(const uint8_t uid[8], SpoolTagData &out);
inline bool pn5180ReadNfcvOpenSpool(const uint8_t uid[8], SpoolTagData &out);
// Needed by pn5180ReadSpoolEx's optional capacity output (nfcvOpenSpool only).
inline int pn5180NfcvUserBytes(const uint8_t uid[8], uint8_t *bsOut = nullptr, uint8_t *nbOut = nullptr);
// Needed by pn5180Probe's optional CC read (debug view only, see readCc param below).
inline bool pn5180NtagReadPages(uint8_t startPage, int count, uint8_t *out);
inline bool pn5180NtagCcIsVirgin(const uint8_t cc[4], bool &alreadyNdefOut);
inline bool pn5180NfcvReadBlock(const uint8_t uid[8], uint8_t block, uint8_t out[4]);
inline bool pn5180NfcvCcIsVirgin(const uint8_t cc[4], bool &alreadyNdefOut);
// Needed by pn5180Probe's page-count read (debug view only, NFC-A/NTAG branch).
enum NtagVariant { NTAG_UNKNOWN = 0, NTAG_213, NTAG_215, NTAG_216 };
inline int ntagUserBytes(NtagVariant v);
inline NtagVariant pn5180NtagGetVersion();

// --- Combined debug probe: NFC-V first, then NFC-A --------------------------
// Always leaves the reader back in ISO15693 mode, so the normal (debug-off) poll
// keeps working without a restart.
// Also attempts the databaseId parse (idParsed/idText) exactly like the real read path
// (pn5180ReadSpool) would -- so the WebUI/TFT debug view shows precisely what the
// normal flow would see (e.g. "no valid ID -> would fall back to a UID lookup").
//
// readCc (default false, only the debug-mode caller in main.cpp passes true, and only
// on a UID change): also reads the Capability Container (out.ccState) for NFC-A/NFC-V.
// Done INLINE here, while the card is already selected, rather than as a separate
// pn5180ProbeCcState() re-select afterwards -- an earlier version did exactly that and
// caused a real bug: the extra reset()+setupRF()+re-select cycle right after this
// function's own reset()+setupRF() was enough RF churn to occasionally corrupt the
// NEXT poll's anticollision read (observed live: a truncated 3-byte UID instead of the
// full 4, logged as a spurious extra "new tag" event). Reading the CC before the first
// reset() avoids the extra cycle entirely.
inline bool pn5180Probe(PN5180ProbeResult &out, bool readCc = false) {
  out = PN5180ProbeResult();
  if (!g_pn5180Ready || !g_pn5180) return false;

  // 1) NFC-V (ISO15693) — the reader's normal resting mode.
  uint8_t uidRaw[8] = {0};
  ISO15693ErrorCode rcV = g_pn5180->getInventory(uidRaw);
  g_pn5180LastRc = (int)rcV;
  if (rcV == ISO15693_EC_OK) {
    g_pn5180OkCount++;
    out.type = PN5180_TAG_NFCV;
    char buf[3];
    for (int i = 7; i >= 0; i--) { snprintf(buf, sizeof(buf), "%02X", uidRaw[i]); out.uid += buf; }
    uint8_t bs = 0, nb = 0, uidTmp[8];
    memcpy(uidTmp, uidRaw, 8);
    if (g_pn5180->getSystemInfo(uidTmp, &bs, &nb, &out.dsfid, &out.dsfidPresent,
                                 &out.afi, &out.afiPresent,
                                 &out.icRef, &out.icRefPresent) == ISO15693_EC_OK) {
      out.blockSize = bs; out.numBlocks = nb;
    }
    pn5180ReadNfcvId(uidRaw, out.idParsed, out.idText);  // best effort, debug view only
    if (readCc) {
      uint8_t cc[4];
      memcpy(uidTmp, uidRaw, 8);
      if (pn5180NfcvReadBlock(uidTmp, /*NFCV_OS_CC_BLOCK=*/0, cc)) {
        bool alreadyNdef;
        bool virgin = pn5180NfcvCcIsVirgin(cc, alreadyNdef);
        // pn5180NfcvCcIsVirgin only recognizes the 4-byte-CC magic (0xE1); a foreign
        // tag could carry the 8-byte form (0xE2, see HARDWARE.md) -- also "ndef" here
        // even though we only ever write the 4-byte form ourselves.
        out.ccState = virgin ? "virgin" : (alreadyNdef || cc[0] == 0xE2) ? "ndef" : "other";
      }
    }
    return true;
  }
  g_pn5180->reset();
  g_pn5180->setupRF();

  // 2) NFC-A (ISO14443-A) — temporarily switch the reader to type-A.
  bool foundA = pn5180ProbeNfcA(out);
  if (foundA) {
    bool isClassic = (out.sak == 0x08 || out.sak == 0x18 || out.sak == 0x09 || out.sak == 0x28);
    if (isClassic) {
      pn5180ReadMifareId(out.uid, out.idParsed, out.idText);
      // Mifare Classic has no CC concept -- out.ccState stays "".
      // Block count is fixed per SAK (sector layout is fully determined by the chip
      // variant, no on-tag query needed): 1K = 16 sectors x 4 blocks, 4K = 32x4 + 8x16,
      // Mini = 5 sectors x 4 blocks. The ISO14443-4 case (SAK 0x28) isn't a fixed Mifare
      // Classic layout, so it's left unset rather than guessed.
      if (out.sak == 0x08) { out.numPages = 64; out.numPagesPresent = true; }
      else if (out.sak == 0x18) { out.numPages = 256; out.numPagesPresent = true; }
      else if (out.sak == 0x09) { out.numPages = 20; out.numPagesPresent = true; }
    } else {
      // GET_VERSION FIRST, before any READ. Order matters and cost a while to pin down:
      // this used to sit after pn5180ReadNtagId() below and timed out every single time
      // (both attempts, back to back), so the debug view kept reporting the conservative
      // NTAG213 fallback for an actual NTAG215. A plain READ (0x30) ends the window in
      // which the tag still answers GET_VERSION (0x60), so it has to go directly after
      // the SELECT -- which is exactly what pn5180WriteNtagOpenSpool does, and why the
      // write path always got the variant right while this one never did.
      NtagVariant variant = pn5180NtagGetVersion();
      if (variant != NTAG_UNKNOWN) {
        out.numPages = ntagUserBytes(variant) / 4 + 4;  // user pages + pages 0-3 (UID/lock/CC)
        out.numPagesPresent = true;
      }
      pn5180ReadNtagId(out.idParsed, out.idText);  // card still selected
      if (readCc) {
        uint8_t cc[4];
        if (pn5180NtagReadPages(3, 1, cc)) {
          bool alreadyNdef;
          bool virgin = pn5180NtagCcIsVirgin(cc, alreadyNdef);
          out.ccState = virgin ? "virgin" : alreadyNdef ? "ndef" : "other";
        }
      }
    }
  }

  g_pn5180->reset();  // back to ISO15693 mode (for the next V poll / normal operation)
  g_pn5180->setupRF();

  return foundA;
}

// --- Read the databaseId off a tag (both types) ------------------------------
// Parses the legacy ID layout: ASCII decimal digits followed by space/NUL padding to
// the full field width -- exactly what pn5180WriteNtagId/pn5180WriteMifareId/
// pn5180WriteNfcvId produce (digits, then ' ' padding out to PN5180_ID_BYTES).
// Returns the parsed ID (>=0) or -1. textOut = the visible raw characters (for the UI).
//
// The trailing bytes are VALIDATED, not just used as a terminator. They used to be
// treated as "stop here, whatever follows" -- which made any foreign tag carrying
// leading ASCII digits parse as one of our IDs. A real case: an NTAG with an inventory
// number "81" + spaces on page 4 and a foreign NDEF CC reported idParsed=81, i.e. a
// third-party tag claiming to be spool 81 (see also the occupancy cross-check in
// pn5180ApplyIdTrust, which this function deliberately does NOT do itself -- it has no
// access to the CC and only judges the field's own shape).
//
// This cannot make the legacy layout self-describing: it carries no magic, so digits
// with correct padding stay indistinguishable from a foreign tag that happens to look
// the same. It only rejects the shapes our writers can never produce. Callers that need
// the stronger judgement must combine this with occupancy (see PN5180ProbeResult::
// idSource / pn5180ApplyIdTrust).
static long pn5180ParseIdBytes(const uint8_t *bytes, int len, String &textOut) {
  textOut = "";
  String digits = "";
  int i = 0;
  for (; i < len; i++) {
    char c = (char)bytes[i];
    if (c >= '0' && c <= '9') { digits += c; textOut += c; }
    else break;
  }
  if (digits.length() == 0) return -1;
  // The digit run must END inside the buffer, i.e. at least one padding byte must be
  // visible. Digits running up to the last byte mean the field was truncated and the
  // value is a PREFIX of the real id -- "1234567890" read as 8 bytes yields 12345678,
  // a different, plausible-looking, entirely wrong spool. Callers pass a variable
  // length here (pn5180ReadNfcvId passes however many bytes it managed to read), so
  // this is reachable in practice, not just in theory.
  if (i >= len) { textOut = ""; return -1; }
  // Everything after the digits must be padding (space or NUL). Our writers pad with
  // ' '; an erased/short field reads back NUL. Anything else -- another digit run, a
  // letter, binary -- is not our layout.
  for (; i < len; i++) {
    char c = (char)bytes[i];
    if (c != ' ' && c != 0) { textOut = ""; return -1; }
  }
  // A leading zero is never produced by String(long) for a value we wrote, so "0081"
  // is somebody else's fixed-width field, not our ID. Plain "0" stays valid.
  if (digits.length() > 1 && digits[0] == '0') { textOut = ""; return -1; }
  // 10 digits is the widest uint32; more cannot be one of our IDs and would overflow
  // toInt() silently.
  if (digits.length() > 10) { textOut = ""; return -1; }
  return digits.toInt();
}

// Cross-checks a legacy-parsed id against the tag's occupancy and downgrades it when
// the two disagree. This is the one place the two judgements meet: the ID parser reads
// a fixed offset and knows nothing about the CC, while occupancy reads the CC and knows
// nothing about the ID field. Until this existed they could contradict each other in a
// single /nfcprobe response -- occupancy "foreign" (this is somebody else's format)
// next to idParsed 81 (this is our spool 81), which is what the SpoolManager plugin ran
// into on a third-party NTAG carrying an inventory number.
//
// Only "legacy" ids are downgraded. An "extended" id matched a real magic, so a
// "foreign" occupancy next to it means the occupancy heuristic was wrong, not the id --
// occupancy only inspects the CC and the first user page, which an Extended tag does
// not use the way an NDEF tag does.
//
// The id is NOT cleared: /nfcprobe is a diagnostic endpoint and "there are digits here,
// but they are not credible" is more useful than a bare -1, which cannot be told apart
// from an empty field. Callers decide what to do with an "unverified" id; the load flow
// refuses it (see main.cpp's flowWouldUse).
inline void pn5180ApplyIdTrust(long idParsed, const String &occupancy,
                               bool hasExtended, String &idSourceOut) {
  // hasExtended is tested BEFORE idParsed, deliberately. On an Extended tag the legacy
  // area holds the format's own header, not digits -- an ntagExtended page 4 reads
  // "OX\x03\x00", which pn5180ParseIdBytes correctly refuses, leaving idParsed at -1.
  // The id is still on the tag, in the Extended payload. Testing idParsed first made
  // "extended" unreachable on exactly the path that reports the raw legacy parse (the
  // NFC-debug poll branch assigns the probe result wholesale, while the normal branch
  // substitutes the Extended id first), so turning NFC debug on silently downgraded a
  // verified tag to "". A trust field that depends on a debug toggle is worse than no
  // trust field, since a consumer cannot tell the two apart.
  // Both conditions, not hasExtended alone: a format can be verified AND carry no
  // OctoScale id. TigerTag is the live case (pn5180ReadSpoolExOpt's TigerTag branch
  // sets hasExtended without touching idOut, deliberately -- the format has no
  // databaseId field), and OpenPrintTag behaves the same way. Reporting "extended"
  // there would claim a trustworthy id next to idParsed == -1, which is a promise the
  // tag cannot keep.
  if (hasExtended && idParsed >= 0) { idSourceOut = "extended"; return; }
  // Verified format, no id of ours on it. Distinct from "" (nothing readable at all):
  // a consumer must not fall back to a UID lookup here and then offer to write the
  // tag, because there IS structured foreign data on it.
  if (hasExtended) { idSourceOut = "extendedNoId"; return; }
  if (idParsed < 0) { idSourceOut = ""; return; }
  idSourceOut = (occupancy == "foreign") ? "unverified" : "legacy";
}

// NFC-A/NTAG: read the ID pages via READ (0x30). Requires the card to already be
// selected (call right after pn5180ProbeNfcA, which leaves CRC on). READ always
// returns 4 pages (16 bytes) from the given page; 12 ID bytes fit starting at page 4.
inline bool pn5180ReadNtagId(long &idOut, String &textOut) {
  PN5180 *p = g_pn5180;
  idOut = -1; textOut = "";
  // CRC must be on (NTAG READ carries CRC) — left that way by ProbeNfcA's SELECT.
  p->clearIRQStatus(0xffffffff);
  p->writeRegisterWithAndMask(SYSTEM_CONFIG, 0xfffffff8);
  p->writeRegisterWithOrMask(SYSTEM_CONFIG, 0x00000003);
  uint8_t rd[2] = { 0x30, PN5180_ID_START_PAGE };  // READ from the user page
  if (!p->sendData(rd, 2, 0)) return false;
  if (!pn5180WaitRx(p, 15)) return false;
  uint32_t rxStatus = 0;
  p->readRegister(RX_STATUS, &rxStatus);
  uint16_t n = (uint16_t)(rxStatus & 0x1ff);
  if (n < PN5180_ID_BYTES) return false;   // NTAG READ returns 16 bytes
  uint8_t *data = p->readData(n > 16 ? 16 : n);
  if (!data) return false;
  idOut = pn5180ParseIdBytes(data, PN5180_ID_BYTES, textOut);
  return true;
}

// NFC-V/ISO15693: read the ID from the first blocks (the library's readSingleBlock).
// Block size comes from getSystemInfo (usually 4). Requires the tag to be in the field.
inline bool pn5180ReadNfcvId(const uint8_t *uidLsb, long &idOut, String &textOut) {
  idOut = -1; textOut = "";
  uint8_t blockSize = 4, numBlocks = 0;
  uint8_t uidTmp[8];
  memcpy(uidTmp, uidLsb, 8);
  if (g_pn5180->getSystemInfo(uidTmp, &blockSize, &numBlocks) != ISO15693_EC_OK) {
    blockSize = 4;  // fallback: most ICODE tags use 4-byte blocks
  }
  if (blockSize == 0 || blockSize > 32) blockSize = 4;
  uint8_t idBytes[PN5180_ID_BYTES];
  int got = 0;
  uint8_t blk = PN5180_ID_START_BLOCK;
  while (got < PN5180_ID_BYTES) {
    uint8_t block[32];
    memcpy(uidTmp, uidLsb, 8);
    if (g_pn5180->readSingleBlock(uidTmp, blk, block, blockSize) != ISO15693_EC_OK)
      break;
    for (int i = 0; i < blockSize && got < PN5180_ID_BYTES; i++)
      idBytes[got++] = block[i];
    blk++;
  }
  if (got == 0) return false;
  // `got`, not PN5180_ID_BYTES: only the bytes actually read are passed. A short read
  // (a block failed mid-field) must not be padded out with stale stack bytes, and
  // pn5180ParseIdBytes rejects a digit run that reaches the end of what it was given,
  // so a truncated field yields -1 rather than a prefix of the real id.
  idOut = pn5180ParseIdBytes(idBytes, got, textOut);
  return true;
}

// Combined: detects the tag type and reads the databaseId, then leaves the reader back
// in ISO15693 mode. Returns true = a tag was present (even without a valid ID).
//   typeOut = detected type, idOut = ID (>=0) or -1, uidHexOut/textOut for the UI.
inline bool pn5180ReadSpool(PN5180TagType &typeOut, long &idOut,
                            String &uidHexOut, String &textOut) {
  typeOut = PN5180_TAG_NONE; idOut = -1; uidHexOut = ""; textOut = "";
  if (!g_pn5180Ready || !g_pn5180) return false;

  // 1) NFC-V first (normal mode). getInventory returns the UID (LSB-first).
  uint8_t uid[8] = {0};
  ISO15693ErrorCode rc = g_pn5180->getInventory(uid);
  g_pn5180LastRc = (int)rc;
  if (rc == ISO15693_EC_OK) {
    g_pn5180OkCount++;
    typeOut = PN5180_TAG_NFCV;
    char b[3];
    for (int i = 7; i >= 0; i--) { snprintf(b, sizeof(b), "%02X", uid[i]); uidHexOut += b; }
    pn5180ReadNfcvId(uid, idOut, textOut);  // ID from blocks (best effort)
    g_pn5180->reset(); g_pn5180->setupRF();
    return true;
  }
  g_pn5180->reset(); g_pn5180->setupRF();

  // 2) NFC-A: probe (selects the card), then read the ID -- NTAG/Ultralight (plain
  // READ) or, for Mifare Classic, an authenticated block read (Crypto1, factory key).
  PN5180ProbeResult pr;
  if (pn5180ProbeNfcA(pr)) {
    typeOut = PN5180_TAG_NFCA;
    uidHexOut = pr.uid;
    bool isClassic = (pr.sak == 0x08 || pr.sak == 0x18 || pr.sak == 0x09 || pr.sak == 0x28);
    if (isClassic) pn5180ReadMifareId(pr.uid, idOut, textOut);  // best effort, wrong/no key -> idOut stays -1
    else pn5180ReadNtagId(idOut, textOut);                      // card is still selected
    g_pn5180->reset(); g_pn5180->setupRF();
    return true;
  }
  g_pn5180->reset(); g_pn5180->setupRF();
  return false;
}

// Extended entry point (plan C.3): tries the richer per-type formats first (Mifare
// Extended, NTAG OpenSpool), falling back to the legacy ID-only read when a tag has no
// Extended payload (no magic / no valid NDEF) or is NFC-V (never had an Extended
// format planned for it). Deliberately NOT called from the 500ms poll loop directly --
// it does 1-3 extra authenticated block reads or NDEF page reads on top of the
// existing probe, which is wasted work on every poll for a tag that isn't changing.
// Callers should only invoke this once per UID change and cache the result (see
// main.cpp's poll loop). data.databaseId mirrors idOut for callers that only care
// about the legacy field.
// formatOut (optional): the Extended format actually found on the tag, when
// hasExtended -- only meaningful for NFC-V, where either nfcvExtended or nfcvOpenSpool
// could be present (Mifare/NTAG have exactly one Extended format each, so the caller
// can infer it from typeOut/SAK without this). Left untouched when hasExtended is false.
// capacityBytesOut (optional): for an nfcvOpenSpool tag, the tag's real capacity (see
// pn5180NfcvUserBytes) -- lets the UI show the actual NDEF budget instead of
// nfcClassifyTag()'s nfcvExtended-sized default. Left untouched otherwise.
inline bool pn5180ReadSpoolEx(PN5180TagType &typeOut, long &idOut, String &uidHexOut,
                              String &textOut, SpoolTagData &data, bool &hasExtended,
                              String *formatOut = nullptr, int *capacityBytesOut = nullptr) {
  data = SpoolTagData();
  hasExtended = false;
  if (!pn5180ReadSpool(typeOut, idOut, uidHexOut, textOut)) return false;

  if (typeOut == PN5180_TAG_NFCA) {
    PN5180ProbeResult pr;
    if (pn5180ProbeNfcA(pr)) {
      bool isClassic = (pr.sak == 0x08 || pr.sak == 0x18 || pr.sak == 0x09 || pr.sak == 0x28);
      if (isClassic) {
        if (pn5180ReadMifareExtended(pr.uid, data)) { hasExtended = true; idOut = data.databaseId; }
      } else {
        // Try both NTAG formats -- disjoint page ranges (Extended's magic sits at
        // pages 4-5, OpenSpool's NDEF TLV starts at page 4 too but with a different
        // first-byte check: 0x03 for the TLV tag vs. 'O' for Extended's magic), same
        // "each format's own check rejects the other's data" pattern as NFC-V below.
        if (pn5180ReadNtagExtended(data)) {
          hasExtended = true; idOut = data.databaseId;
          if (formatOut) *formatOut = "ntagExtended";
        } else if (pn5180ReadNtagOpenSpool(data)) {
          hasExtended = true; idOut = data.databaseId;
          if (formatOut) *formatOut = "openSpool";
        } else if (pn5180ReadNtagTigerTag(data)) {
          // Foreign format, carries no OctoScale databaseId -- idOut stays whatever
          // pn5180ReadSpool() found (typically -1/unparsable on a real TigerTag tag,
          // since it has no ASCII-decimal ID at page 4). hasExtended still flips true
          // so the caller knows structured data (material/brand/... IDs) is present.
          hasExtended = true;
          if (formatOut) *formatOut = "tigerTag";
        }
      }
      g_pn5180->reset(); g_pn5180->setupRF();
    }
  } else if (typeOut == PN5180_TAG_NFCV) {
    // Extended blocks are UID-addressed, no session/selection needed -- but the raw
    // (LSB-first) UID is required, not uidHexOut's display-order hex string, so re-run
    // getInventory rather than parsing the hex back (order would have to be reversed
    // and is easy to get wrong).
    uint8_t rawUid[8] = {0};
    if (g_pn5180->getInventory(rawUid) == ISO15693_EC_OK) {
      // Try both formats -- they occupy disjoint blocks (nfcvExtended's magic sits at
      // blocks 3-4, nfcvOpenSpool's NDEF TLV starts at block 1) and each format's own
      // magic-byte/TLV-tag check rejects the other's data, so at most one of these two
      // calls succeeds for any real tag.
      if (pn5180ReadNfcvExtended(rawUid, data)) {
        hasExtended = true; idOut = data.databaseId;
        if (formatOut) *formatOut = "nfcvExtended";
      } else if (pn5180ReadNfcvOpenSpool(rawUid, data)) {
        hasExtended = true; idOut = data.databaseId;
        if (formatOut) *formatOut = "nfcvOpenSpool";
        if (capacityBytesOut) *capacityBytesOut = pn5180NfcvUserBytes(rawUid);
      }
      g_pn5180->reset(); g_pn5180->setupRF();
    }
  }
  if (!hasExtended) data.databaseId = idOut;  // keep the two id fields consistent either way
  return true;
}

// --- Write the databaseId to an NFC-A/NTAG tag -------------------------------
// NFC-A/NTAG only — NFC-V is deliberately never written (those tags could be
// factory-provisioned). Writes the ID as ASCII decimal, space-padded, across 3 pages
// (4-6) via NTAG WRITE (0xA2 <page> <4 bytes>), each page verified.
// Returns true = written + verified. errOut carries the reason on failure.
inline bool pn5180WriteNtagId(long id, String &errOut) {
  errOut = "";
  dbgLogf("NTAG write: start id=%ld", id);
  if (!g_pn5180Ready || !g_pn5180) { errOut = "reader not ready"; return false; }
  if (id < 0) { errOut = "invalid ID"; return false; }

  String s = String(id);
  // 10, not PN5180_ID_BYTES: the field is 12 bytes wide, but pn5180ParseIdBytes only
  // accepts up to 10 digits (the widest uint32) AND requires at least one padding byte
  // after them. A wider value would be written and verified here, then read back as -1
  // for the rest of the tag's life. Keep this bound and the parser's in step.
  if ((int)s.length() > 10) { errOut = "ID too long"; return false; }
  uint8_t idbuf[PN5180_ID_BYTES];
  for (int i = 0; i < PN5180_ID_BYTES; i++)
    idbuf[i] = (i < (int)s.length()) ? (uint8_t)s[i] : (uint8_t)' ';

  // Select the NFC-A card (CRC left on from SELECT).
  dbgLog("NTAG write: probing NFC-A...");
  PN5180ProbeResult pr;
  if (!pn5180ProbeNfcA(pr)) {
    g_pn5180->reset(); g_pn5180->setupRF();
    errOut = "no NFC-A tag";
    dbgLog("NTAG write: no NFC-A tag found, aborting");
    return false;
  }
  dbgLogf("NTAG write: probe OK, uid=%s atqa=0x%04X sak=0x%02X", pr.uid.c_str(), pr.atqa, pr.sak);
  // NTAG WRITE (0xA2) only exists on Type-2 tags (NTAG/Ultralight). Mifare Classic
  // uses sector auth + a different command set -> reject early with a clear reason
  // instead of a cryptic low-level write/verify failure.
  if ((pr.sak & 0x20) || (pr.sak & ~0x04) != 0x00) {
    g_pn5180->reset(); g_pn5180->setupRF();
    errOut = String("unsupported tag (") + pn5180NfcaProduct(pr.atqa, pr.sak) +
             "): only NTAG/Ultralight can be written";
    dbgLogf("NTAG write: rejected, %s", errOut.c_str());
    return false;
  }
  PN5180 *p = g_pn5180;
  uint32_t rxStatus = 0;
  bool ok = true;

  // Write 3 pages of 4 bytes each, verifying by reading back. Each page starts with a
  // full reset+re-select of the tag: reusing the transceiver across consecutive
  // WRITE/READ frames left it stuck reporting transceiveState=3 ("wait receive") no
  // matter how often Idle/Transceive was re-armed -> a full RF reset is what reliably
  // clears it (the initial ProbeNfcA + this reset+re-select pattern are the only two
  // reset paths that have been confirmed to work).
  for (int page = 0; page < PN5180_ID_BYTES / 4; page++) {
    if (page > 0) {
      dbgLogf("NTAG write: page %d -> re-select tag", page);
      g_pn5180->reset(); g_pn5180->setupRF();
      PN5180ProbeResult pr2;
      if (!pn5180ProbeNfcA(pr2)) { ok = false; errOut = "lost tag between pages"; dbgLog("NTAG write: re-select failed"); break; }
    }
    dbgLogf("NTAG write: page %d -> write", page);
    uint8_t wr[6] = { 0xA2, (uint8_t)(PN5180_ID_START_PAGE + page),
                      idbuf[page*4+0], idbuf[page*4+1], idbuf[page*4+2], idbuf[page*4+3] };
    p->clearIRQStatus(0xffffffff);
    p->writeRegisterWithAndMask(SYSTEM_CONFIG, 0xfffffff8);
    p->writeRegisterWithOrMask(SYSTEM_CONFIG, 0x00000003);
    if (!pn5180SendDataRetry(p, wr, 6)) { ok = false; errOut = "write send error"; dbgLog("NTAG write: sendData(write) failed"); break; }
    dbgLog("NTAG write: sendData(write) OK, waiting for ACK");
    pn5180WaitRx(p, 15);  // NTAG ACKs WRITE with a 4-bit ACK (0x0A); a short wait suffices

    // Verify: read back the page just written.
    dbgLogf("NTAG write: page %d -> verify read", page);
    p->clearIRQStatus(0xffffffff);
    p->writeRegisterWithAndMask(SYSTEM_CONFIG, 0xfffffff8);
    p->writeRegisterWithOrMask(SYSTEM_CONFIG, 0x00000003);
    uint8_t rd[2] = { 0x30, (uint8_t)(PN5180_ID_START_PAGE + page) };
    if (!pn5180SendDataRetry(p, rd, 2)) { ok = false; errOut = "verify send error"; dbgLog("NTAG write: sendData(verify) failed"); break; }
    dbgLog("NTAG write: sendData(verify) OK, waiting for RX");
    if (!pn5180WaitRx(p, 15)) { ok = false; errOut = "verify timeout"; dbgLog("NTAG write: verify RX timeout"); break; }
    p->readRegister(RX_STATUS, &rxStatus);
    dbgLogf("NTAG write: RX_STATUS=0x%08X (len=%u)", rxStatus, (unsigned)(rxStatus & 0x1ff));
    if ((uint16_t)(rxStatus & 0x1ff) < 4) { ok = false; errOut = "verify too short"; dbgLog("NTAG write: verify reply too short"); break; }
    dbgLog("NTAG write: calling readData(4)...");
    uint8_t *rb = p->readData(4);
    dbgLogf("NTAG write: readData returned %s", rb ? "ptr" : "NULL");
    if (!rb) { ok = false; errOut = "verify read error"; break; }
    for (int i = 0; i < 4; i++)
      if (rb[i] != idbuf[page*4+i]) { ok = false; errOut = "verify mismatch"; break; }
    dbgLogf("NTAG write: page %d %s", page, ok ? "verified OK" : "MISMATCH");
    if (!ok) break;
  }

  dbgLogf("NTAG write: done, ok=%d err=%s", ok, errOut.c_str());
  g_pn5180->reset(); g_pn5180->setupRF();  // back to normal ISO15693 operation
  return ok;
}

// --- NTAG variant detection + generic page read/write (C.2) -------------------
// NTAG21x variants differ in user memory size, which OpenSpool/NDEF writing needs to
// know up front (how many pages are available for the NDEF message). Enum + these two
// functions are forward-declared above pn5180Probe, which also needs them (debug view's
// page-count read) but runs earlier in the file than this section.
inline int ntagUserBytes(NtagVariant v) {
  switch (v) { case NTAG_213: return 144; case NTAG_215: return 504; case NTAG_216: return 888; default: return 144; }
}
inline const char *ntagVariantName(NtagVariant v) {
  switch (v) { case NTAG_213: return "ntag213"; case NTAG_215: return "ntag215"; case NTAG_216: return "ntag216"; default: return "unknown"; }
}

// GET_VERSION (0x60): an 8-byte response, byte 6 = storage size code. Requires the
// card to already be selected. On timeout/NAK (some Ultralight variants don't support
// this command, or a marginal RF link drops it) falls back conservatively to NTAG213
// (144 B) rather than guessing bigger and overrunning the tag's actual capacity.
//
// Observed live on a real NTAG215 (debug log) that the FIRST GET_VERSION right after a
// card selection consistently timed out while later calls in the same session usually
// succeeded -- looks like the card needs a brief settle time post-select. A bare retry
// helped in the debug-poll path (which already runs pn5180ReadNtagId first, giving the
// card a few ms before this function's first attempt) but NOT reliably in the write
// path (pn5180WriteNtagOpenSpool calls this immediately after pn5180ProbeNfcA's SELECT,
// with nothing in between -- both retry attempts landed inside that same too-early
// window and both timed out). Fixed at the root instead of papering over it with more
// retries: a short settle delay before the FIRST attempt only (a failed attempt's own
// ~15 ms wait already provides that gap for any later attempts).
// Without this, a first-call timeout silently downgraded a 504 B NTAG215 to a 144 B
// budget for the rest of that write, which showed up as extra dropped fields
// (density/weights/temperatures) on a tag that had plenty of room for all of them.
inline NtagVariant pn5180NtagGetVersion() {
  PN5180 *p = g_pn5180;
  for (int attempt = 0; attempt < 2; attempt++) {
    if (attempt == 0) delay(2);
    p->clearIRQStatus(0xffffffff);
    p->writeRegisterWithAndMask(SYSTEM_CONFIG, 0xfffffff8);
    p->writeRegisterWithOrMask(SYSTEM_CONFIG, 0x00000003);
    uint8_t cmd[1] = { 0x60 };
    if (!p->sendData(cmd, 1, 0)) { dbgLogf("NTAG GET_VERSION: send failed (attempt %d)", attempt); continue; }
    if (!pn5180WaitRx(p, 15)) { dbgLogf("NTAG GET_VERSION: timeout (attempt %d)", attempt); continue; }
    uint32_t rxStatus = 0;
    p->readRegister(RX_STATUS, &rxStatus);
    uint16_t n = (uint16_t)(rxStatus & 0x1ff);
    if (n < 8) { dbgLogf("NTAG GET_VERSION: short reply (%u B, attempt %d)", n, attempt); continue; }
    uint8_t *data = p->readData(8);
    if (!data) { dbgLogf("NTAG GET_VERSION: readData failed (attempt %d)", attempt); continue; }
    dbgLogf("NTAG GET_VERSION: %02X %02X %02X %02X %02X %02X %02X %02X",
            data[0], data[1], data[2], data[3], data[4], data[5], data[6], data[7]);
    switch (data[6]) {
      case 0x0F: return NTAG_213;
      case 0x11: return NTAG_215;
      case 0x13: return NTAG_216;
      default:   return NTAG_213;  // unrecognized code -> conservative default
    }
  }
  dbgLog("NTAG GET_VERSION: failed after retry, defaulting to 213");
  return NTAG_213;
}

// Reads `count` consecutive 4-byte pages starting at `startPage` into out (4*count
// bytes). One READ (0x30) returns 4 pages (16 B) regardless of how many were asked
// for, so this only issues ceil(count/4) transceives -- cheap compared to writes
// (which each need a full reset+re-select, see pn5180WriteNtagId's comment).
inline bool pn5180NtagReadPages(uint8_t startPage, int count, uint8_t *out) {
  PN5180 *p = g_pn5180;
  int got = 0;
  while (got < count) {
    p->clearIRQStatus(0xffffffff);
    p->writeRegisterWithAndMask(SYSTEM_CONFIG, 0xfffffff8);
    p->writeRegisterWithOrMask(SYSTEM_CONFIG, 0x00000003);
    uint8_t rd[2] = { 0x30, (uint8_t)(startPage + got) };
    if (!p->sendData(rd, 2, 0)) return false;
    if (!pn5180WaitRx(p, 15)) return false;
    uint32_t rxStatus = 0;
    p->readRegister(RX_STATUS, &rxStatus);
    uint16_t n = (uint16_t)(rxStatus & 0x1ff);
    if (n < 4) return false;
    uint8_t *data = p->readData(n > 16 ? 16 : n);
    if (!data) return false;
    int pagesGot = min(4, count - got);
    memcpy(out + got * 4, data, pagesGot * 4);
    got += pagesGot;
  }
  return true;
}

// Writes ONE 4-byte page (WRITE 0xA2), with a full reset+re-select first (except for
// the very first page of a run, where the caller has already just selected the tag) --
// same pattern pn5180WriteNtagId uses, required because reusing the transceiver across
// consecutive WRITE/READ frames gets stuck at transceiveState=3. No verify-read here
// (callers that need verification do their own read-back); kept minimal since this is
// called many times in a row for NDEF writes.
inline bool pn5180NtagWritePage(const String &uidHex, uint8_t page, const uint8_t data[4],
                                bool reselect, String &errOut) {
  PN5180 *p = g_pn5180;
  if (reselect) {
    g_pn5180->reset(); g_pn5180->setupRF();
    PN5180ProbeResult pr2;
    if (!pn5180ProbeNfcA(pr2) || pr2.uid != uidHex) { errOut = "lost tag while writing"; return false; }
  }
  uint8_t wr[6] = { 0xA2, page, data[0], data[1], data[2], data[3] };
  p->clearIRQStatus(0xffffffff);
  p->writeRegisterWithAndMask(SYSTEM_CONFIG, 0xfffffff8);
  p->writeRegisterWithOrMask(SYSTEM_CONFIG, 0x00000003);
  if (!pn5180SendDataRetry(p, wr, 6)) { errOut = "write send error"; return false; }
  pn5180WaitRx(p, 15);  // NTAG ACKs WRITE with a 4-bit ACK (0x0A); a short wait suffices
  return true;
}

// Parses a big-endian hex UID string (as produced by pn5180ProbeNfcA's out.uid) back
// into raw bytes. Mifare Classic 1K almost always has a 4-byte single-size UID (SAK
// 0x08 already implies this) -> only that case is supported here.
inline bool pn5180UidHexToBytes4(const String &hex, uint8_t out[4]) {
  if (hex.length() != 8) return false;
  for (int i = 0; i < 4; i++) {
    char b[3] = { hex[i*2], hex[i*2+1], 0 };
    out[i] = (uint8_t)strtoul(b, nullptr, 16);
  }
  return true;
}

// NFC-V counterpart of the 4-byte helper above. pn5180Probe builds the ISO15693 UID
// string big-endian (byte 7 first, the usual display order), so decoding it back into
// the little-endian byte array the PN5180 library expects means reversing as we go --
// feeding a straight-order array to readSingleBlock addresses a different (nonexistent)
// tag and every block read fails.
inline bool pn5180UidHexToBytes8Reversed(const String &hex, uint8_t out[8]) {
  if (hex.length() != 16) return false;
  for (int i = 0; i < 8; i++) {
    char b[3] = { hex[i*2], hex[i*2+1], 0 };
    out[7 - i] = (uint8_t)strtoul(b, nullptr, 16);
  }
  return true;
}

// Authenticates the sector containing `block` against the currently-selected tag's UID.
// Must be called with the tag freshly selected (right after pn5180ProbeNfcA) --
// authentication is bound to the current RF session and is lost on reset()/setupRF().
//
// key/authMode default to the factory Key A (FFFFFFFFFFFF), which is what OctoScale's
// own tags use and what every existing caller wants. Pass a different key to read a tag
// keyed by somebody else -- foreign vendor tags derive theirs from the UID, so the key
// is supplied per call rather than stored anywhere on the device.
inline bool pn5180MifareAuth(const String &uidHex, uint8_t block, String &errOut,
                             const uint8_t *key = MIFARE_KEY_A,
                             uint8_t authMode = MIFARE_AUTH_KEY_A) {
  uint8_t uid4[4];
  if (!pn5180UidHexToBytes4(uidHex, uid4)) { errOut = "unsupported UID length for Mifare auth"; return false; }
  uint8_t status = 0xFF;
  bool ok = g_pn5180->mifareAuthenticate(block, key, authMode, uid4, &status);
  // Only log FAILED auths unconditionally. A tag resting on the reader re-authenticates
  // on every 500 ms poll, so logging every success buried everything else in the ring
  // buffer within a couple of minutes -- successes are only traced when explicitly
  // asked for via /nfcauthtrace (same switch the raw SPI frame dump uses).
  if (!ok || status != 0 || g_pn5180AuthTrace)
    dbgLogf("Mifare auth: block=%u status=0x%02X ok=%d", block, status, ok);
  if (!ok || status != 0) { errOut = "auth failed (wrong key or tag rejected)"; return false; }
  return true;
}

// Reads one already-authenticated Mifare Classic block (16 bytes) into out[16].
// Card must be selected AND the sector containing `block` already authenticated in
// this RF session (see pn5180MifareAuth). Returns false on any transport/length error.
inline bool pn5180MifareReadBlock(uint8_t block, uint8_t out[16]) {
  PN5180 *p = g_pn5180;
  p->clearIRQStatus(0xffffffff);
  p->writeRegisterWithAndMask(SYSTEM_CONFIG, 0xfffffff8);
  p->writeRegisterWithOrMask(SYSTEM_CONFIG, 0x00000003);
  uint8_t rd[2] = { 0x30, block };
  if (!p->sendData(rd, 2, 0)) return false;
  if (!pn5180WaitRx(p, 15)) return false;
  uint32_t rxStatus = 0;
  p->readRegister(RX_STATUS, &rxStatus);
  uint16_t n = (uint16_t)(rxStatus & 0x1ff);
  if (n < 16) return false;
  uint8_t *data = p->readData(16);
  if (!data) return false;
  memcpy(out, data, 16);
  return true;
}

// --- Raw sector/block dump (unknown-tag fallback for the NFC debug view) -----
// Mifare Classic 1K only. Authenticates each sector in turn with the factory-default
// Key A (FFFFFFFFFFFF -- the only key OctoScale ever writes, and what most foreign
// tags/vendor tools still ship with) and reads every data block. Sector trailer
// blocks (3, 7, 11, ... every 4th block) hold the Key A/B + access bits -- never
// dumped as hex (no reason to expose key material even read-back, and it's not
// content anyway), only whether that sector authenticated.
struct MifareBlockDump {
  uint8_t block = 0;
  bool sectorAuthOk = false;
  bool readOk = false;
  uint8_t data[16] = {0};
};

// Full-image variant: 64 entries (every block including sector trailers) rather than
// the 48 data blocks above. Parameters cover what the debug dump and a foreign-tag read
// each need, so there is only one auth+read loop to maintain:
//
//   keyA/keyB   16 keys of 6 bytes each, indexed by sector; nullptr = factory Key A
//               everywhere. Key A is tried first, Key B only if Key A is rejected --
//               vendor tags vary in which one guards the data.
//   sectorMask  bit N set = dump sector N. 0xFFFF = all 16. Skipping sectors a parser
//               doesn't need is the single biggest saving available: block reads, not
//               auth, dominate the runtime (measured 765 ms with zero successful reads
//               vs. ~2150 ms reading all blocks).
//   withTrailers  keep sector-trailer blocks in the output. They hold key material, so
//               the debug view passes false; a raw consumer that computes over the full
//               1K image needs them present (zero-filled if unreadable) and passes true.
//
// Returns the number of entries written. Never aborts early: a sector whose key is
// rejected yields entries with sectorAuthOk=false and zeroed data, so a partial result
// is still usable -- some parsers only need one sector.
inline int pn5180DumpMifareClassic1kEx(const String &uidHex, MifareBlockDump *out,
                                       const uint8_t (*keyA)[6] = nullptr,
                                       const uint8_t (*keyB)[6] = nullptr,
                                       uint16_t sectorMask = 0xFFFF,
                                       bool withTrailers = false) {
  int n = 0;
  for (uint8_t sector = 0; sector < 16; sector++) {
    if (!(sectorMask & (1u << sector))) continue;
    uint8_t trailerBlock = sector * 4 + 3;
    // Authenticate against the sector's first DATA block, not its trailer. Crypto1 auth
    // is sector-wide, so either address unlocks the same sector -- but measured on a
    // real 1K tag (UID 0B06703B, factory key), a trailer-addressed auth never gets a
    // response back: every sector returned the uninitialised status 0xFF, including the
    // two that reported ok=1, so even those were transport artefacts rather than
    // successful authentications. The same key and mode against block 4 answers
    // status=0x00 on every single poll, which is why the normal read path
    // (pn5180ReadMifareExtended, block 4/8/12/16/36) always worked on the very tag whose
    // dump failed completely. That contradiction stood unexplained since 2026-08-29.
    uint8_t authBlock = sector * 4;
    String authErr;
    // Key A first, then Key B -- a rejected key costs one failed auth, and the tag
    // stays selected only as long as auth succeeds, so the retry re-selects below.
    bool authOk = pn5180MifareAuth(uidHex, authBlock, authErr,
                                   keyA ? keyA[sector] : MIFARE_KEY_A, MIFARE_AUTH_KEY_A);
    if (!authOk && keyB) {
      // A failed auth drops the card out of the selected state -- without re-selecting,
      // the Key B attempt would fail for the wrong reason and look like a bad key.
      PN5180ProbeResult reselect;
      if (pn5180ProbeNfcA(reselect) && reselect.uid == uidHex)
        authOk = pn5180MifareAuth(uidHex, authBlock, authErr,
                                  keyB[sector], MIFARE_AUTH_KEY_B);
    }
    uint8_t lastBlock = withTrailers ? trailerBlock : (uint8_t)(trailerBlock - 1);
    for (uint8_t b = sector * 4; b <= lastBlock; b++) {
      out[n].block = b;
      out[n].sectorAuthOk = authOk;
      out[n].readOk = authOk && pn5180MifareReadBlock(b, out[n].data);
      n++;
    }
  }
  return n;
}

// Debug-view dump: 48 data blocks, factory key, no trailers (they hold key material and
// aren't content). Thin wrapper so there is one auth+read implementation, not two.
inline int pn5180DumpMifareClassic1k(const String &uidHex, MifareBlockDump out[47]) {
  return pn5180DumpMifareClassic1kEx(uidHex, out);
}

// NTAG / Ultralight raw dump -- the keyless counterpart to the Mifare dump above.
// No authentication exists on these tags, so this is a plain page walk from page 0.
//
// Starting at page 0 (not at the user area, page 4) is deliberate and must not be
// "optimised" away: consumers index absolute page offsets, and a shifted dump corrupts
// their parsing silently rather than failing loudly. Pages 0-3 are UID/lock bytes and
// the Capability Container.
//
// Reads stop at the first failing page rather than erroring out -- Ultralight variants
// differ in size and the honest answer is "this is how far the tag goes". Returns the
// number of PAGES read (4 bytes each); 0 means even page 0 was unreadable.
// Requires the card to already be selected (call right after pn5180ProbeNfcA).
inline int pn5180DumpNtagPages(uint8_t *out, int maxPages) {
  int got = 0;
  // One READ returns 4 pages, so walk in blocks of 4 and keep whatever came back.
  while (got < maxPages) {
    int want = min(4, maxPages - got);
    if (!pn5180NtagReadPages((uint8_t)got, want, out + got * 4)) break;
    got += want;
  }
  return got;
}

// NFC-V (ISO15693) raw dump -- the third dump path alongside Mifare Classic and NTAG.
// No authentication exists here either (ISO15693 has no Crypto1 concept), so this is a
// plain UID-addressed block walk from block 0.
//
// Starting at block 0 is deliberate, same reasoning as the NTAG walk above: consumers
// index absolute block offsets, and a shifted dump corrupts their parsing silently.
// Block 0 is the Capability Container on an NDEF-formatted tag.
//
// Reads stop at the first failing block rather than erroring out -- ICODE variants
// differ in size and getSystemInfo's numBlocks is not always trustworthy, so the honest
// answer is "this is how far the tag actually goes". Returns the number of BLOCKS read
// (blockSize bytes each, almost always 4); 0 means even block 0 was unreadable.
// Requires a prior successful getInventory (the UID is passed in explicitly).
inline int pn5180DumpNfcvBlocks(const uint8_t uid[8], uint8_t *out, int maxBlocks) {
  int got = 0;
  while (got < maxBlocks) {
    if (!pn5180NfcvReadBlock(uid, (uint8_t)got, out + got * NFCV_BLOCK_SIZE)) break;
    got++;
  }
  return got;
}

// NTAG/Ultralight counterpart to pn5180MifareOccupancy below. These tags have no keys,
// so the Capability Container (page 3) plus the first user page carry the answer:
// an all-zero CC means the tag was never written, an NDEF CC (0xE1) with an empty
// message area likewise, and anything else is somebody's data.
//
// This exists because the normal poll path uses pn5180ReadSpool(), which never reads
// the CC -- so without this, occupancy stayed blank for every NTAG outside debug mode
// and the overwrite protection silently did not apply to them.
//
// Returns "empty", "foreign", or "" when it could not be determined (transport error).
// Requires the card to already be selected (call right after pn5180ProbeNfcA).
inline String pn5180NtagOccupancy() {
  // 8 PAGES, not 8 bytes: pages 0-7 = UID/lock (0-2), CC (3), first user pages (4-7).
  // This was uint8_t[8] and pn5180NtagReadPages wrote 32 bytes into it -- a 24-byte
  // stack overflow that tripped the canary ("Stack smashing protect failure") and
  // rebooted the device, but only sometimes: whether it crashed or silently corrupted
  // the neighbouring frame depended on what happened to sit there. Sized in bytes here
  // (pages * 4) so the unit is explicit and the two numbers cannot drift apart again.
  uint8_t pages[8 * 4];
  if (!pn5180NtagReadPages(0, 8, pages)) return "";
  const uint8_t *cc = pages + 3 * 4;
  bool alreadyNdef = false;
  if (pn5180NtagCcIsVirgin(cc, alreadyNdef)) return "empty";  // never written
  // A formatted-but-unused NDEF tag reads as an empty TLV: 0x03 0x00 (message of
  // length zero) or a plain 0x00/0xFE terminator right at the start of the user area.
  if (alreadyNdef) {
    const uint8_t *u = pages + 4 * 4;
    bool emptyMsg = (u[0] == 0x00) || (u[0] == 0xFE) || (u[0] == 0x03 && u[1] == 0x00);
    return emptyMsg ? "empty" : "foreign";
  }
  return "foreign";  // non-virgin, non-NDEF CC -> somebody else formatted this
}

// NFC-V (ISO15693) counterpart to pn5180NtagOccupancy/pn5180MifareOccupancy. Fills the
// third carrier's occupancy, which used to stay "" unconditionally: the poll path had no
// block reader when this was written, so a blank ISO15693 tag was indistinguishable from
// a vendor-written one. That gap surfaced as a real user-visible bug -- SpoolManager-
// Extended falls back to a heuristic when occupancy is empty ("no Extended data + no
// spool id + a recognised tag type" -> assume vendor tag), which fires on every blank
// NFC-V tag and warned the user about overwriting a vendor tag that was their own blank.
//
// Three-way, NOT a plain all-zero scan. An all-zero test looks correct and is wrong:
// a factory-NDEF-formatted-but-empty tag carries a CC plus a terminator TLV, so it is
// not all-zero and would be reported "foreign" -- exactly the case that was being
// misreported. Measured on a real blank ICODE (UID E00401532560D3EA): all blocks zero
// EXCEPT block 23 (283C0000) and block 27 (000000FE, the NDEF terminator). Same
// CC-driven reasoning pn5180NtagOccupancy already uses.
//
// Returns "empty", "foreign", or "" when it could not be determined (transport error).
// Requires a prior successful getInventory (the UID is passed in explicitly).
inline String pn5180NfcvOccupancy(const uint8_t uid[8]) {
  uint8_t cc[4];
  if (!pn5180NfcvReadBlock(uid, 0, cc)) return "";  // transport error -> unknown, stay silent
  bool alreadyNdef = false;
  if (pn5180NfcvCcIsVirgin(cc, alreadyNdef)) return "empty";  // all-zero CC -> never written
  // NDEF-formatted: 4-byte CC magic 0xE1, or the 8-byte form 0xE2 a foreign tag may use
  // (we only ever write the 4-byte one). Empty message = a terminator or a zero-length
  // TLV right at the start of the data area, same shapes pn5180NtagOccupancy tests for.
  if (alreadyNdef || cc[0] == 0xE2) {
    uint8_t first[4];
    if (!pn5180NfcvReadBlock(uid, 1, first)) return "";
    bool emptyMsg = (first[0] == 0x00) || (first[0] == 0xFE) ||
                    (first[0] == 0x03 && first[1] == 0x00);
    return emptyMsg ? "empty" : "foreign";
  }
  return "foreign";  // non-virgin, non-NDEF CC -> somebody else formatted this
}

// Tells a blank Mifare Classic tag apart from one carrying a foreign vendor's data,
// for the case where no format we know could parse it. Mifare has no Capability
// Container to inspect (unlike NTAG/NFC-V), so this leans on the key instead: every
// tag OctoScale writes keeps the factory-default Key A, so a sector that REJECTS that
// key was re-keyed by somebody else and must never be treated as free space. If the
// key still works, the tag is readable and genuinely empty only when its data blocks
// are all-zero -- a re-used tag with leftover bytes counts as foreign too.
//
// Returns "empty", "foreign", or "" when it could not be determined (transport error).
// Requires the card to already be selected (call right after pn5180ProbeNfcA).
inline String pn5180MifareOccupancy(const String &uidHex) {
  String authErr;
  // Sector 1 (trailer block 7) rather than sector 0: block 0 is the read-only
  // manufacturer block and sector 0 often keeps the default key even on vendor tags,
  // so it is the least informative sector to ask.
  if (!pn5180MifareAuth(uidHex, 7, authErr)) return "foreign";  // re-keyed -> not ours
  for (uint8_t b = 4; b < 7; b++) {
    uint8_t data[16];
    if (!pn5180MifareReadBlock(b, data)) return "";  // transport error -> unknown, stay silent
    for (int i = 0; i < 16; i++) if (data[i] != 0x00) return "foreign";
  }
  return "empty";
}

// --- Chip-level health/diagnostic status (NOT tag-related -- readable even with no
// tag on the reader). Pulls the handful of PN5180-internal EEPROM/register values the
// project reads at boot (product/firmware version) but never otherwise exposes, plus a
// few more that are useful for telling "reader hardware is unhappy" apart from "no tag
// present": die ID (a per-chip serial, handy for a multi-unit fleet), EEPROM layout
// version, RF field/transceiver state, and the two coarse status registers.
//
// SYSTEM_STATUS/TEMP_CONTROL are shown as raw hex + the one bit each that NXP's PN5180
// datasheet documents with certainty (system mode in bits 0-2 of SYSTEM_STATUS;
// overtemperature warning in bit 0 of TEMP_CONTROL) -- deliberately not decoding
// further undocumented bits into named flags we can't verify against real hardware.
struct PN5180ChipStatus {
  bool ok = false;                 // false = the reader wasn't ready, nothing below is valid
  uint8_t dieId[16] = {0};         // EEPROM 0x00, 16 bytes, unique per chip
  uint8_t eepromVersion[2] = {0};  // EEPROM 0x14 (major, minor)
  uint32_t rfStatus = 0;           // register 0x1d, raw
  bool rfFieldOn = false;          // RF_STATUS bit 0
  PN5180TransceiveStat transceiveState = PN5180_TS_Idle;  // RF_STATUS bits 24-26
  uint32_t systemStatus = 0;       // register 0x24, raw
  uint8_t systemMode = 0;          // SYSTEM_STATUS bits 0-2 (0=idle,1=standby,2=active/RW,3=LPCD,7=Autocoll)
  uint32_t tempControl = 0;        // register 0x25, raw
  bool overtempWarning = false;    // TEMP_CONTROL bit 0
  uint32_t irqStatus = 0;          // current IRQ_STATUS snapshot (register 0x02), raw
};

inline PN5180ChipStatus pn5180ReadChipStatus() {
  PN5180ChipStatus s;
  if (!g_pn5180Ready || !g_pn5180) return s;
  PN5180 *p = g_pn5180;
  s.ok = p->readEEprom(DIE_IDENTIFIER, s.dieId, sizeof(s.dieId))
      && p->readEEprom(EEPROM_VERSION, s.eepromVersion, sizeof(s.eepromVersion))
      && p->readRegister(RF_STATUS, &s.rfStatus)
      && p->readRegister(SYSTEM_STATUS, &s.systemStatus)
      && p->readRegister(TEMP_CONTROL, &s.tempControl);
  s.rfFieldOn = s.rfStatus & 0x01;
  s.transceiveState = p->getTransceiveState();
  s.systemMode = s.systemStatus & 0x07;
  s.overtempWarning = s.tempControl & 0x01;
  s.irqStatus = p->getIRQStatus();
  return s;
}

// --- Read the databaseId off a Mifare Classic 1K tag -------------------------
// Requires the card to already be selected (call right after pn5180ProbeNfcA).
// Authenticates sector 1 (Key A) then plain-reads block 4 (16 bytes, ID left-padded
// with spaces same as the NTAG/NFC-V layout).
inline bool pn5180ReadMifareId(const String &uidHex, long &idOut, String &textOut) {
  PN5180 *p = g_pn5180;
  idOut = -1; textOut = "";
  String authErr;
  if (!pn5180MifareAuth(uidHex, MIFARE_ID_BLOCK, authErr)) return false;

  p->clearIRQStatus(0xffffffff);
  p->writeRegisterWithAndMask(SYSTEM_CONFIG, 0xfffffff8);
  p->writeRegisterWithOrMask(SYSTEM_CONFIG, 0x00000003);
  uint8_t rd[2] = { 0x30, MIFARE_ID_BLOCK };  // READ (encrypted -- chip decrypts transparently)
  if (!p->sendData(rd, 2, 0)) return false;
  if (!pn5180WaitRx(p, 15)) return false;
  uint32_t rxStatus = 0;
  p->readRegister(RX_STATUS, &rxStatus);
  uint16_t n = (uint16_t)(rxStatus & 0x1ff);
  if (n < PN5180_ID_BYTES) return false;
  uint8_t *data = p->readData(n > 16 ? 16 : n);
  if (!data) return false;
  idOut = pn5180ParseIdBytes(data, PN5180_ID_BYTES, textOut);
  return true;
}

// Writes one 16-byte Mifare Classic block, with verify-read, and reports the reason on
// failure. The sector containing `block` must already be authenticated in this RF
// session (see pn5180MifareAuth) -- this helper does NOT authenticate itself, so
// callers writing multiple blocks in the same sector only need to authenticate once.
//
// Mifare Classic WRITE is a TWO-step protocol (unlike NTAG's single write frame):
//  1. send [0xA0, block] -> tag ACKs with a 4-bit 0x0A if it accepts the command
//  2. send the 16 data bytes -> tag ACKs again once they're actually written
// Sending command+data in one frame (the NTAG pattern) never gets step 1's ACK, so the
// tag silently ignores the write -> the read-back below then times out.
inline bool pn5180MifareWriteBlock(uint8_t block, const uint8_t data[16], String &errOut) {
  PN5180 *p = g_pn5180;
  bool ok = true;
  dbgLog("Mifare write: writing block " + String(block));
  uint8_t wr[2] = { 0xA0, block };
  p->clearIRQStatus(0xffffffff);
  p->writeRegisterWithAndMask(SYSTEM_CONFIG, 0xfffffff8);
  p->writeRegisterWithOrMask(SYSTEM_CONFIG, 0x00000003);
  uint8_t dataCopy[16];
  memcpy(dataCopy, data, 16);  // pn5180SendDataRetry wants non-const
  if (!pn5180SendDataRetry(p, wr, 2)) { ok = false; errOut = "write cmd send error"; dbgLog("Mifare write: sendData(cmd) failed"); }
  if (ok && !pn5180WaitRx(p, 15)) { ok = false; errOut = "write cmd ACK timeout"; dbgLog("Mifare write: no ACK after write command"); }
  if (ok) {
    dbgLog("Mifare write: cmd ACKed, sending 16 data bytes");
    p->clearIRQStatus(0xffffffff);
    p->writeRegisterWithAndMask(SYSTEM_CONFIG, 0xfffffff8);
    p->writeRegisterWithOrMask(SYSTEM_CONFIG, 0x00000003);
    if (!pn5180SendDataRetry(p, dataCopy, 16)) { ok = false; errOut = "write data send error"; dbgLog("Mifare write: sendData(data) failed"); }
    else if (!pn5180WaitRx(p, 15)) { ok = false; errOut = "write data ACK timeout"; dbgLog("Mifare write: no ACK after data"); }
  }

  if (ok) {
    dbgLog("Mifare write: verify read");
    uint8_t rb[16];
    if (!pn5180MifareReadBlock(block, rb)) { ok = false; errOut = "verify read error"; }
    else if (memcmp(rb, data, 16) != 0) { ok = false; errOut = "verify mismatch"; }
  }
  dbgLogf("Mifare write: block %u done, ok=%d err=%s", block, ok, errOut.c_str());
  return ok;
}

// --- Write the databaseId to a Mifare Classic 1K tag --------------------------
// One 16-byte block fits PN5180_ID_BYTES (12) with 4 bytes to spare (space-padded) --
// unlike NTAG, no multi-page split is needed. Writes+verifies block 4 (sector 1),
// factory Key A. Rejects tags whose SAK doesn't say "Mifare Classic" (see
// pn5180NfcaProduct) so a stray NTAG never takes this path by accident.
inline bool pn5180WriteMifareId(long id, String &errOut) {
  errOut = "";
  dbgLogf("Mifare write: start id=%ld", id);
  if (!g_pn5180Ready || !g_pn5180) { errOut = "reader not ready"; return false; }
  if (id < 0) { errOut = "invalid ID"; return false; }

  String s = String(id);
  // 10, not PN5180_ID_BYTES: the field is 12 bytes wide, but pn5180ParseIdBytes only
  // accepts up to 10 digits (the widest uint32) AND requires at least one padding byte
  // after them. A wider value would be written and verified here, then read back as -1
  // for the rest of the tag's life. Keep this bound and the parser's in step.
  if ((int)s.length() > 10) { errOut = "ID too long"; return false; }
  uint8_t idbuf[16];
  for (int i = 0; i < 16; i++)
    idbuf[i] = (i < (int)s.length()) ? (uint8_t)s[i] : (uint8_t)' ';

  dbgLog("Mifare write: probing NFC-A...");
  PN5180ProbeResult pr;
  if (!pn5180ProbeNfcA(pr)) {
    g_pn5180->reset(); g_pn5180->setupRF();
    errOut = "no NFC-A tag";
    dbgLog("Mifare write: no NFC-A tag found, aborting");
    return false;
  }
  dbgLogf("Mifare write: probe OK, uid=%s atqa=0x%04X sak=0x%02X", pr.uid.c_str(), pr.atqa, pr.sak);
  // Only Mifare Classic (SAK 0x08/0x18/0x28, or the ISO14443-4 smartcard bit) takes
  // this path -- reject Type-2 tags (NTAG/Ultralight) with a clear reason instead of a
  // confusing "auth failed" from trying Crypto1 on a tag that doesn't support it.
  bool isClassic = (pr.sak == 0x08 || pr.sak == 0x18 || pr.sak == 0x09 || pr.sak == 0x28);
  if (!isClassic) {
    g_pn5180->reset(); g_pn5180->setupRF();
    errOut = String("unsupported tag (") + pn5180NfcaProduct(pr.atqa, pr.sak) +
             "): only Mifare Classic can be written on this path";
    dbgLogf("Mifare write: rejected, %s", errOut.c_str());
    return false;
  }

  String authErr;
  bool ok = pn5180MifareAuth(pr.uid, MIFARE_ID_BLOCK, authErr);
  if (!ok) errOut = authErr;
  else ok = pn5180MifareWriteBlock(MIFARE_ID_BLOCK, idbuf, errOut);

  dbgLogf("Mifare write: done, ok=%d err=%s", ok, errOut.c_str());
  g_pn5180->reset(); g_pn5180->setupRF();  // back to normal ISO15693 operation
  return ok;
}

// --- Mifare Classic Extended format (C.1) -------------------------------------
// Sector 1/block 4 = legacy ID anchor (unchanged, written by pn5180WriteMifareId).
// Sector 2 (blocks 8-9) = numeric fields + CRC-8. Sector 3 (blocks 12-14) = strings.
// Confirmed live (multi-sector auth spike): a Crypto1 auth for one sector survives,
// without reset()/setupRF(), long enough to authenticate + read/write a second and
// third sector in the same RF session.
//
// Block 8 layout (16 B, little-endian multi-byte fields):
//   [0]    'O'            magic byte 0
//   [1]    'S'            magic byte 1
//   [2]    format version (0x02+: block 10 holds bed temp min/max)
//   [3]    flags          bit0 = strings present (sector 3 written)
//   [4-7]  databaseId     uint32
//   [8-9]  totalWeight    uint16, grams (0xFFFF = not set)
//   [10-11] spoolWeight   uint16, grams (0xFFFF = not set)
//   [12-13] usedWeight    uint16, grams (0xFFFF = not set)
//   [14-15] density       uint16, g/cm3 * 1000 (0xFFFF = not set)
// Block 9 layout (16 B):
//   [0-1]  diameter            uint16, mm * 1000 (0xFFFF = not set)
//   [2-3]  diameterTolerance   uint16, mm * 1000 (0xFFFF = not set)
//   [4]    hotend temp         uint8, deg C (0xFF = not set)
//   [5]    bed temp            uint8, deg C (0xFF = not set)
//   [6]    enclosure temp      uint8, deg C (0xFF = not set)
//   [7]    hotend offset       int8, deg C
//   [8]    bed offset          int8, deg C
//   [9]    enclosure offset    int8, deg C
//   [10-12] color RGB          3 B (0,0,0 if unparseable/multi-color/sentinel)
//   [13]   hotend temp min     uint8, deg C (0xFF = not set) -- v2+, was "reserved"
//   [14]   hotend temp max     uint8, deg C (0xFF = not set) -- v2+, was "reserved"
//   [15]   CRC-8 (poly 0x07) over block8[0..15] + block9[0..14] + block10[0..1] -- v2+
// Block 10 layout (16 B, v2+; unused/unallocated on v1 tags):
//   [0]    bed temp min        uint8, deg C (0xFF = not set)
//   [1]    bed temp max        uint8, deg C (0xFF = not set)
//   [2-15] reserved            0x00
//
// Blocks 12-14 (sector 3): a flat 48-byte buffer of length-prefixed UTF-8 strings
// ([len][bytes]...), in order vendor, material, colorName. A field that doesn't fit is
// simply omitted (len=0) rather than truncating badly mid-run -- callers can tell what
// was dropped by comparing input vs. what pn5180ReadMifareExtended reads back.

// Minute-of-day (0..1439) <-> uint16. Deliberately NOT routed through pn5180ScaleU16:
// this value has a hard valid range, and anything outside it is a bug in the caller
// rather than a large-but-real measurement. Out-of-range is stored as "not set" instead
// of being wrapped or clamped to 1439, because a wrong time of day is worse than none.
// Two representations, deliberately: 0xFFFF is the ON-TAG "not set" (uint16 has no
// negative), -1 is the in-RAM/JSON one every other SpoolTagData number already uses.
// The conversion happens here, so /nfcprobe reports -1 like all its sibling fields
// rather than leaking the raw wire sentinel into the API.
inline uint16_t pn5180MinuteOfDayU16(int v) {
  return (v >= 0 && v <= 1439) ? (uint16_t)v : 0xFFFF;
}
inline int pn5180UnscaleMinuteOfDay(uint16_t raw) {
  return (raw <= 1439) ? (int)raw : -1;  // 0xFFFF and any junk -> not set
}

// --- v5 drying/td field codecs (shared by ALL THREE Extended carriers) -------------
// Layout agreed with SpoolManagerExtended: dryingTemperature u8 (0xFF = not set),
// dryingTime u16 LE in MINUTES (0xFFFF), td u16 LE scaled x100 (0xFFFF).
//
// dryingTime deliberately stays in MINUTES on the tag -- our whole API speaks minutes
// (OpenPrintTag spec key 58, /nfcprobe, /nfcwritespool), and every carrier here has room
// for a u16, so there is no reason to convert. That is the direct lesson from TigerTag's
// single hour-byte, where the missing division cost a factor of 60 (see the unit trap in
// lib/../HARDWARE.md). One encode/decode pair, used by all three writers and readers --
// do not open-code these at the call sites.
inline uint8_t pn5180DryTempU8(int degC) {
  return (degC >= 0 && degC <= 0xFE) ? (uint8_t)degC : 0xFF;
}
inline int pn5180UnscaleDryTemp(uint8_t raw) {
  return (raw == 0xFF) ? -1 : (int)raw;
}
inline uint16_t pn5180DryTimeU16(int minutes) {
  return (minutes >= 0 && minutes <= 0xFFFE) ? (uint16_t)minutes : 0xFFFF;
}
inline int pn5180UnscaleDryTime(uint16_t raw) {
  return (raw == 0xFFFF) ? -1 : (int)raw;
}
// td is a dimensionless opacity number (0.1 = most opaque .. 100 = most transparent),
// stored x100 so one decimal survives. Never label it mm.
inline uint16_t pn5180TdU16(float td) {
  if (td < 0) return 0xFFFF;
  long scaled = lroundf(td * 100.0f);
  return (scaled >= 0 && scaled <= 0xFFFE) ? (uint16_t)scaled : 0xFFFF;
}
inline float pn5180UnscaleTd(uint16_t raw) {
  return (raw == 0xFFFF) ? -1.0f : (float)raw / 100.0f;
}
// Little-endian u16 helpers -- the v5 fields are LE on every carrier.
inline void pn5180PutU16LE(uint8_t *p, uint16_t v) { p[0] = (uint8_t)(v & 0xFF); p[1] = (uint8_t)(v >> 8); }
inline uint16_t pn5180GetU16LE(const uint8_t *p) { return (uint16_t)(p[0] | ((uint16_t)p[1] << 8)); }

inline uint16_t pn5180ScaleU16(float v, float scale, uint16_t notSet = 0xFFFF) {
  if (v < 0) return notSet;
  long scaled = lroundf(v * scale);
  if (scaled < 0 || scaled > 0xFFFE) return notSet;
  return (uint16_t)scaled;
}
inline float pn5180UnscaleU16(uint16_t v, float scale, uint16_t notSet = 0xFFFF) {
  if (v == notSet) return -1;
  return (float)v / scale;
}

// usedWeight and remainingWeight are not independent: the database keeps them so that
// used + remaining == totalWeight. Rounding each to whole grams on its own breaks that
// -- 646.6 and 353.4 both round up and the tag then claims 1001 g on a 1000 g spool,
// a total the spool never had. So round usedWeight and derive remainingWeight from it,
// which keeps the sum exact and holds each field within half a gram of the database.
// Only applies when all three values are present; with totalWeight or either component
// missing there is nothing to reconcile and both fall back to plain rounding.
inline void pn5180ScaleWeightPair(float usedWeight, float remainingWeight, float totalWeight,
                                  uint16_t &usedOut, uint16_t &remainingOut) {
  usedOut = pn5180ScaleU16(usedWeight, 1.0f);
  remainingOut = pn5180ScaleU16(remainingWeight, 1.0f);
  if (usedWeight < 0 || remainingWeight < 0 || totalWeight < 0) return;
  uint16_t totU = pn5180ScaleU16(totalWeight, 1.0f);
  if (totU == 0xFFFF || usedOut == 0xFFFF || remainingOut == 0xFFFF) return;
  if ((uint32_t)usedOut + remainingOut == totU) return;  // already consistent
  // Derive the second field rather than rounding it. Guarded against a pair that
  // doesn't belong to this total (a stale tag value paired with a fresh one): the
  // correction is only applied when it stays within one gram of what was measured.
  long derived = (long)totU - (long)usedOut;
  if (derived < 0 || derived > 0xFFFE) return;
  if (fabsf((float)derived - remainingWeight) > 1.0f) return;
  remainingOut = (uint16_t)derived;
}

// Same not-set-sentinel convention as the u16 pair above, for fields needing more than
// 16 bits of range (totalLength/usedLength, mm -- a 16-bit limit would cap filament
// length at ~65 m, too small for real spools). 3 bytes LE, 0xFFFFFF reserved as the
// sentinel (matches the u16 helpers reserving their top value, 0xFFFF/0xFFFE split).
inline uint32_t pn5180ScaleU24(long v, uint32_t notSet = 0xFFFFFF) {
  if (v < 0 || v > 0xFFFFFE) return notSet;
  return (uint32_t)v;
}
inline long pn5180UnscaleU24(uint32_t v, uint32_t notSet = 0xFFFFFF) {
  if (v == notSet) return -1;
  return (long)v;
}
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
